sgbmzm/Halacha-T-S3/drivers/miriam25.py

# -*- coding: utf-8 -*-
# Converted from miriam.ttf using:
#     ./font2bitmap.py miriam.ttf -s 'abcdefghijklmnopqrstuvwxyzABCDEFGHIJKLMNOPQRSTUVWXYZ0123456789!#°{ }$%&'"'"'()*;<=>@#~^$!?+,-:./אבגדהוזחטיכךלמםנןסעפףצץקרשת' 25

MAP = (
    'abcdefghijklmnopqrstuvwxyzABCDEF'
    'GHIJKLMNOPQRSTUVWXYZ0123456789!#'
    '°{ }$%&\'()*;<=>@#~^$!?+,-:./אבג'
    'דהוזחטיכךלמםנןסעפףצץקרשת'
)

BPP = 1
HEIGHT = 23
MAX_WIDTH = 23
_WIDTHS = \
    b'\x0d\x0d\x0b\x0d\x0d\x07\x0d\x0d\x05\x07\x0b\x05\x13\x0d\x0d\x0d'\
    b'\x0d\x08\x0b\x06\x0d\x0b\x10\x0b\x0b\x0b\x0f\x0f\x10\x10\x0f\x0e'\
    b'\x12\x10\x06\x0b\x0f\x0d\x13\x10\x12\x0f\x12\x10\x0f\x0e\x10\x0f'\
    b'\x15\x0f\x0f\x0e\x0c\x0c\x0c\x0c\x0c\x0c\x0c\x0c\x0c\x0c\x07\x0a'\
    b'\x0a\x0c\x07\x0c\x0c\x12\x10\x07\x08\x08\x0c\x08\x0e\x0f\x0e\x17'\
    b'\x0a\x0e\x0a\x0c\x07\x09\x0f\x07\x07\x07\x07\x0a\x0f\x0d\x0a\x0c'\
    b'\x0f\x08\x08\x0e\x0e\x08\x0d\x0c\x0d\x0e\x0e\x08\x07\x0d\x0e\x0d'\
    b'\x0d\x0d\x0c\x0d\x0c\x10\x0f'

OFFSET_WIDTH = 2
_OFFSETS = \
    b'\x00\x00\x01\x2b\x02\x56\x03\x53\x04\x7e\x05\xa9\x06\x4a\x07\x75'\
    b'\x08\xa0\x09\x13\x09\xb4\x0a\xb1\x0b\x24\x0c\xd9\x0e\x04\x0f\x2f'\
    b'\x10\x5a\x11\x85\x12\x3d\x13\x3a\x13\xc4\x14\xef\x15\xec\x17\x5c'\
    b'\x18\x59\x19\x56\x1a\x53\x1b\xac\x1d\x05\x1e\x75\x1f\xe5\x21\x3e'\
    b'\x22\x80\x24\x1e\x25\x8e\x26\x18\x27\x15\x28\x6e\x29\x99\x2b\x4e'\
    b'\x2c\xbe\x2e\x5c\x2f\xb5\x31\x53\x32\xc3\x34\x1c\x35\x5e\x36\xce'\
    b'\x38\x27\x3a\x0a\x3b\x63\x3c\xbc\x3d\xfe\x3f\x12\x40\x26\x41\x3a'\
    b'\x42\x4e\x43\x62\x44\x76\x45\x8a\x46\x9e\x47\xb2\x48\xc6\x49\x67'\
    b'\x4a\x4d\x4b\x33\x4c\x47\x4c\xe8\x4d\xfc\x4f\x10\x50\xae\x52\x1e'\
    b'\x52\xbf\x53\x77\x54\x2f\x55\x43\x55\xfb\x57\x3d\x58\x96\x59\xd8'\
    b'\x5b\xe9\x5c\xcf\x5e\x11\x5e\xf7\x60\x0b\x60\xac\x61\x7b\x62\xd4'\
    b'\x63\x75\x64\x16\x64\xb7\x65\x58\x66\x3e\x67\x97\x68\xc2\x69\xa8'\
    b'\x6a\xbc\x6c\x15\x6c\xcd\x6d\x85\x6e\xc7\x70\x09\x70\xc1\x71\xec'\
    b'\x73\x00\x74\x2b\x75\x6d\x76\xaf\x77\x67\x78\x08\x79\x33\x7a\x75'\
    b'\x7b\xa0\x7c\xcb\x7d\xf6\x7f\x0a\x80\x35\x81\x49\x82\xb9'

_BITMAPS =\
    b'\x00\x00\x00\x00\x00\x00\x00\x00\x00\x00\x00\x03\xf0\x3f\xc3\x07'\
    b'\x00\x18\x3f\xc3\xfe\x38\x31\x81\x8c\x0c\x70\xe1\xfb\x07\x98\x00'\
    b'\x00\x00\x00\x00\x00\x00\x00\x00\x00\x00\x18\x00\xc0\x06\x00\x30'\
    b'\x01\x9e\x0f\xf8\x78\xe3\x83\x98\x0c\xc0\x66\x03\x30\x19\x81\xce'\
    b'\x1c\x7f\xc3\x3c\x00\x00\x00\x00\x00\x00\x00\x00\x00\x00\x00\x00'\
    b'\x00\x00\x00\x00\x01\xe0\xfe\x18\xe6\x0c\xc0\x18\x03\x00\x60\x0c'\
    b'\x18\xc3\x1f\xc0\xf0\x00\x00\x00\x00\x00\x00\x00\x00\x00\x00\x00'\
    b'\x18\x00\xc0\x06\x00\x30\x3d\x87\xfc\x30\xe3\x83\x18\x18\xc0\xc6'\
    b'\x06\x30\x31\xc1\x86\x1c\x1f\xe0\x7b\x00\x00\x00\x00\x00\x00\x00'\
    b'\x00\x00\x00\x00\x00\x00\x00\x00\x00\x00\x00\x07\xc0\x7f\x07\x1c'\
    b'\x60\x33\x01\x9f\xfc\xff\xe6\x00\x30\x18\xe1\xc3\xfc\x0f\x80\x00'\
    b'\x00\x00\x00\x00\x00\x00\x00\x00\x79\xf3\x06\x3f\x7e\x30\x60\xc1'\
    b'\x83\x06\x0c\x18\x30\x60\x00\x00\x00\x00\x00\x00\x00\x00\x00\x00'\
    b'\x00\x00\x00\x00\x00\x7b\x0f\xf8\x61\xc7\x0e\x30\x31\x81\x8c\x0c'\
    b'\x60\x63\x87\x0c\x38\x7f\xc0\xf6\x30\x31\xc3\x07\xf8\x1f\x00\x00'\
    b'\x00\x00\x00\x06\x00\x30\x01\x80\x0c\x00\x67\x83\xfe\x1c\x38\xc0'\
    b'\xc6\x06\x30\x31\x81\x8c\x0c\x60\x63\x03\x18\x18\xc0\xc0\x00\x00'\
    b'\x00\x00\x00\x00\x00\x00\xc6\x00\x0c\x63\x18\xc6\x31\x8c\x63\x18'\
    b'\x00\x00\x00\x00\x00\x18\x30\x00\x01\x83\x06\x0c\x18\x30\x60\xc1'\
    b'\x83\x06\x0c\x18\x33\xe7\x80\x00\x00\x00\x03\x00\x60\x0c\x01\x80'\
    b'\x30\xe6\x38\xce\x1b\x83\xe0\x7e\x0e\xc1\x8c\x31\xc6\x18\xc3\x98'\
    b'\x38\x00\x00\x00\x00\x00\x00\x00\x63\x18\xc6\x31\x8c\x63\x18\xc6'\
    b'\x31\x8c\x00\x00\x00\x00\x00\x00\x00\x00\x00\x00\x00\x00\x00\x00'\
    b'\x00\x00\x00\x00\x00\x37\xc7\x87\xfb\xf8\xe3\xc3\x98\x30\x33\x06'\
    b'\x06\x60\xc0\xcc\x18\x19\x83\x03\x30\x60\x66\x0c\x0c\xc1\x81\x98'\
    b'\x30\x30\x00\x00\x00\x00\x00\x00\x00\x00\x00\x00\x00\x00\x00\x00'\
    b'\x00\x00\x00\x00\x00\x00\x06\x78\x3f\xe1\xc3\x8c\x0c\x60\x63\x03'\
    b'\x18\x18\xc0\xc6\x06\x30\x31\x81\x8c\x0c\x00\x00\x00\x00\x00\x00'\
    b'\x00\x00\x00\x00\x00\x00\x00\x00\x00\x00\x00\x00\x1f\x03\xfc\x1c'\
    b'\x71\xc1\xcc\x06\x60\x33\x01\x98\x0c\xe0\xe3\x8e\x0f\xe0\x3e\x00'\
    b'\x00\x00\x00\x00\x00\x00\x00\x00\x00\x00\x00\x00\x00\x00\x00\x00'\
    b'\x00\x19\xe0\xff\x87\x8e\x38\x39\x80\xcc\x06\x60\x33\x01\x98\x1c'\
    b'\xe1\xc7\xfc\x37\xc1\x80\x0c\x00\x60\x03\x00\x00\x00\x00\x00\x00'\
    b'\x00\x00\x00\x00\x00\x00\x00\x7b\x07\xf8\x61\xc7\x06\x30\x31\x81'\
    b'\x8c\x0c\x60\x63\x83\x0e\x38\x3f\xc0\xf6\x00\x30\x01\x80\x0c\x00'\
    b'\x60\x00\x00\x00\x00\x00\x00\x03\x73\x83\x03\x03\x03\x03\x03\x03'\
    b'\x03\x03\x03\x00\x00\x00\x00\x00\x00\x00\x00\x00\x00\x00\x00\x00'\
    b'\x00\x07\xc1\xfe\x60\xcc\x01\xc0\x1f\x00\xf8\x03\x98\x33\x8e\x3f'\
    b'\x83\xe0\x00\x00\x00\x00\x00\x00\x00\x01\x0c\x30\xc7\xdf\x30\xc3'\
    b'\x0c\x30\xc3\x0c\x3c\x70\x00\x00\x00\x00\x00\x00\x00\x00\x00\x00'\
    b'\x00\x00\x00\x00\xc0\xc6\x06\x30\x31\x81\x8c\x0c\x60\x63\x03\x18'\
    b'\x18\xc0\xc7\x0e\x1f\xf0\x79\x80\x00\x00\x00\x00\x00\x00\x00\x00'\
    b'\x00\x00\x00\x00\x00\x00\x00\x0c\x06\xc1\x98\x33\x06\x31\x86\x30'\
    b'\xc6\x0d\x81\xb0\x14\x03\x80\x70\x00\x00\x00\x00\x00\x00\x00\x00'\
    b'\x00\x00\x00\x00\x00\x00\x00\x00\x00\x00\x00\x0c\x18\x3e\x18\x76'\
    b'\x3c\x66\x3c\x67\x2c\x63\x24\xc3\x26\xc3\xe6\xc1\xe7\x81\xe7\x81'\
    b'\xc3\x80\xc3\x00\x00\x00\x00\x00\x00\x00\x00\x00\x00\x00\x00\x00'\
    b'\x00\x00\x00\x00\x00\x38\x73\x0c\x33\x07\xe0\x78\x06\x01\xe0\x3c'\
    b'\x0c\xc1\x98\x61\x9c\x38\x00\x00\x00\x00\x00\x00\x00\x00\x00\x00'\
    b'\x00\x00\x00\x00\x03\x01\xb0\x66\x0c\x61\x8c\x21\x8c\x19\x83\x20'\
    b'\x3c\x07\x80\x60\x0c\x03\x80\x60\x7c\x0f\x00\x00\x00\x00\x00\x00'\
    b'\x00\x00\x00\x00\x0f\xf9\xff\x00\xe0\x18\x06\x01\x80\x60\x18\x06'\
    b'\x01\xc0\x3f\xe7\xfc\x00\x00\x00\x00\x00\x00\x00\x00\x00\x00\x00'\
    b'\x03\x80\x07\x00\x1e\x00\x36\x00\xec\x01\x8c\x03\x18\x0c\x38\x18'\
    b'\x30\x7f\xe0\xff\xe1\x80\xc7\x01\xcc\x01\x98\x03\x60\x07\x00\x00'\
    b'\x00\x00\x00\x00\x00\x00\x00\x00\x00\x00\x00\x1f\xf0\x3f\xf8\x60'\
    b'\x38\xc0\x31\x80\x63\x00\xc6\x03\x0f\xfc\x1f\xfc\x30\x1c\x60\x18'\
    b'\xc0\x31\x80\x63\x01\xc7\xff\x0f\xf8\x00\x00\x00\x00\x00\x00\x00'\
    b'\x00\x00\x00\x00\x00\x00\x00\x1f\x00\x7f\xc0\xe0\xe1\x80\x71\x80'\
    b'\x33\x00\x03\x00\x03\x00\x03\x00\x03\x00\x03\x00\x01\x80\x31\x80'\
    b'\x70\xe0\xe0\x7f\xc0\x3f\x00\x00\x00\x00\x00\x00\x00\x00\x00\x00'\
    b'\x00\x00\x00\x00\x01\xff\x01\xff\xc1\x81\xc1\x80\x61\x80\x61\x80'\
    b'\x31\x80\x31\x80\x31\x80\x31\x80\x31\x80\x31\x80\x61\x80\x61\x81'\
    b'\xc1\xff\xc1\xff\x00\x00\x00\x00\x00\x00\x00\x00\x00\x00\x00\x00'\
    b'\x00\x00\x0f\xff\x1f\xfe\x30\x00\x60\x00\xc0\x01\x80\x03\x00\x07'\
    b'\xff\x0f\xfe\x18\x00\x30\x00\x60\x00\xc0\x01\x80\x03\xff\xc7\xff'\
    b'\x80\x00\x00\x00\x00\x00\x00\x00\x00\x00\x00\x00\x00\x3f\xf8\xff'\
    b'\xe3\x00\x0c\x00\x30\x00\xc0\x03\x00\x0f\xf8\x3f\xe0\xc0\x03\x00'\
    b'\x0c\x00\x30\x00\xc0\x03\x00\x0c\x00\x00\x00\x00\x00\x00\x00\x00'\
    b'\x00\x00\x00\x00\x00\x00\x00\x0f\xe0\x0f\xfe\x07\x81\xc3\x80\x38'\
    b'\xc0\x06\x60\x00\x18\x00\x06\x00\x01\x80\xfe\x60\x3f\x98\x00\x63'\
    b'\x00\x18\xe0\x06\x1e\x07\x83\xff\xc0\x3f\x80\x00\x00\x00\x00\x00'\
    b'\x00\x00\x00\x00\x00\x00\x00\x00\x00\x00\xc0\x30\xc0\x30\xc0\x30'\
    b'\xc0\x30\xc0\x30\xc0\x30\xff\xf0\xff\xf0\xc0\x30\xc0\x30\xc0\x30'\
    b'\xc0\x30\xc0\x30\xc0\x30\xc0\x30\xc0\x30\x00\x00\x00\x00\x00\x00'\
    b'\x00\x00\x00\x00\x30\xc3\x0c\x30\xc3\x0c\x30\xc3\x0c\x30\xc3\x0c'\
    b'\x00\x00\x00\x00\x00\x00\x00\x00\xc0\x18\x03\x00\x60\x0c\x01\x80'\
    b'\x30\x06\x00\xc0\x18\x03\x18\x63\x0c\x63\x87\xe0\x78\x00\x00\x00'\
    b'\x00\x00\x00\x00\x00\x00\x00\x00\x0c\x07\x18\x1c\x30\x70\x61\xc0'\
    b'\xc7\x01\x9c\x03\x70\x07\xf0\x0f\x70\x1c\x60\x30\xe0\x60\xe0\xc0'\
    b'\xc1\x81\xc3\x01\xc6\x01\xc0\x00\x00\x00\x00\x00\x00\x00\x00\x00'\
    b'\x00\x00\x01\x80\x0c\x00\x60\x03\x00\x18\x00\xc0\x06\x00\x30\x01'\
    b'\x80\x0c\x00\x60\x03\x00\x18\x00\xc0\x07\xfe\x3f\xf0\x00\x00\x00'\
    b'\x00\x00\x00\x00\x00\x00\x00\x00\x00\x00\x1c\x00\x73\xc0\x1e\x78'\
    b'\x03\xcf\x00\x79\xb0\x1b\x36\x03\x66\x60\xcc\xcc\x19\x99\x83\x33'\
    b'\x18\xc6\x63\x18\xcc\x32\x19\x86\xc3\x30\xd8\x66\x0e\x0c\xc1\xc1'\
    b'\x80\x00\x00\x00\x00\x00\x00\x00\x00\x00\x00\x00\x00\x00\x00\x00'\
    b'\xc0\x30\xe0\x30\xf0\x30\xf0\x30\xd8\x30\xc8\x30\xcc\x30\xc6\x30'\
    b'\xc6\x30\xc3\x30\xc1\x30\xc1\xb0\xc0\xf0\xc0\xf0\xc0\x70\xc0\x30'\
    b'\x00\x00\x00\x00\x00\x00\x00\x00\x00\x00\x00\x00\x00\x00\x00\x3f'\
    b'\x00\x3f\xf0\x1c\x0e\x0e\x01\xc3\x00\x31\x80\x06\x60\x01\x98\x00'\
    b'\x66\x00\x19\x80\x06\x60\x01\x8c\x00\xc3\x80\x70\x70\x38\x0f\xfc'\
    b'\x00\xfc\x00\x00\x00\x00\x00\x00\x00\x00\x00\x00\x00\x00\x00\x00'\
    b'\x00\x1f\xf8\x3f\xf8\x60\x38\xc0\x31\x80\x63\x00\xc6\x03\x8f\xfe'\
    b'\x1f\xf0\x30\x00\x60\x00\xc0\x01\x80\x03\x00\x06\x00\x0c\x00\x00'\
    b'\x00\x00\x00\x00\x00\x00\x00\x00\x00\x00\x00\x00\x00\x00\x7e\x00'\
    b'\x7f\xe0\x38\x1c\x1c\x03\x86\x00\x63\x00\x0c\xc0\x03\x30\x00\xcc'\
    b'\x00\x33\x00\x0c\xc0\x03\x18\x0d\x87\x03\xe0\xf0\x30\x1f\xfe\x01'\
    b'\xf9\xe0\x00\x18\x00\x00\x00\x00\x00\x00\x00\x00\x00\x00\x00\x00'\
    b'\x07\xfe\x07\xff\x06\x03\x86\x01\x86\x01\x86\x01\x86\x03\x07\xff'\
    b'\x07\xfc\x06\x18\x06\x0c\x06\x06\x06\x03\x06\x03\x06\x01\x86\x00'\
    b'\xc0\x00\x00\x00\x00\x00\x00\x00\x00\x00\x00\x00\x00\x00\x07\xe0'\
    b'\x3f\xf0\xe0\x71\x80\x63\x00\x06\x00\x07\x00\x0f\xe0\x07\xf0\x00'\
    b'\xf0\x00\x31\x80\x63\x80\xc3\x83\x03\xfe\x03\xf0\x00\x00\x00\x00'\
    b'\x00\x00\x00\x00\x00\x00\x00\x00\x01\xff\xe7\xff\x80\xc0\x03\x00'\
    b'\x0c\x00\x30\x00\xc0\x03\x00\x0c\x00\x30\x00\xc0\x03\x00\x0c\x00'\
    b'\x30\x00\xc0\x03\x00\x00\x00\x00\x00\x00\x00\x00\x00\x00\x00\x00'\
    b'\x00\x00\xc0\x30\xc0\x30\xc0\x30\xc0\x30\xc0\x30\xc0\x30\xc0\x30'\
    b'\xc0\x30\xc0\x30\xc0\x30\xc0\x30\xc0\x30\xe0\x70\x70\xe0\x7f\xc0'\
    b'\x1f\x80\x00\x00\x00\x00\x00\x00\x00\x00\x00\x00\x00\x00\x00\x18'\
    b'\x00\xd8\x03\x30\x06\x60\x18\x60\x30\xc0\x61\x81\x81\x83\x03\x0c'\
    b'\x02\x18\x06\x60\x0c\xc0\x0d\x80\x1e\x00\x3c\x00\x30\x00\x00\x00'\
    b'\x00\x00\x00\x00\x00\x00\x00\x00\x00\x00\x00\x00\x03\x00\xc0\x78'\
    b'\x0e\x03\x60\x78\x33\x02\xc1\x98\x32\x0c\xc1\x98\x62\x08\xc2\x18'\
    b'\xc2\x30\xc6\x19\x86\x60\xcc\x13\x06\x40\x98\x16\x07\x80\xf0\x3c'\
    b'\x07\x80\xe0\x18\x06\x00\xc0\x00\x00\x00\x00\x00\x00\x00\x00\x00'\
    b'\x00\x00\x00\x00\x00\x00\x00\xe0\x1c\xe0\x70\xe1\xc0\xc3\x00\xcc'\
    b'\x01\xf8\x01\xe0\x01\x80\x07\x80\x0f\x00\x33\x00\xe7\x01\x87\x06'\
    b'\x06\x1c\x0e\x70\x0e\x00\x00\x00\x00\x00\x00\x00\x00\x00\x00\x00'\
    b'\x00\x00\xc0\x0c\xc0\x30\xc0\xc1\xc3\x81\x86\x01\x98\x03\xf0\x03'\
    b'\xc0\x03\x00\x06\x00\x0c\x00\x18\x00\x30\x00\x60\x00\xc0\x01\x80'\
    b'\x00\x00\x00\x00\x00\x00\x00\x00\x00\x00\x00\x00\x01\xff\xe7\xff'\
    b'\x80\x0e\x00\x30\x01\x80\x0c\x00\x60\x03\x00\x1c\x00\x60\x03\x00'\
    b'\x18\x00\xc0\x06\x00\x1f\xfe\x7f\xf8\x00\x00\x00\x00\x00\x00\x00'\
    b'\x00\x00\x00\x00\x00\x00\x00\x03\xe0\xff\x0e\x71\xc3\x98\x19\x81'\
    b'\x98\x19\x81\x98\x19\x81\x9c\x38\xe7\x0f\xf0\x7e\x00\x00\x00\x00'\
    b'\x00\x00\x00\x00\x00\x00\x00\x00\x00\x00\x18\x03\x80\x78\x0f\x80'\
    b'\xd8\x01\x80\x18\x01\x80\x18\x01\x80\x18\x01\x80\x18\x01\x80\x00'\
    b'\x00\x00\x00\x00\x00\x00\x00\x00\x00\x00\x00\x00\x03\xc0\xfe\x1c'\
    b'\x71\x83\x00\x30\x03\x00\x60\x0c\x01\x80\x30\x06\x00\x40\x0f\xf0'\
    b'\xff\x00\x00\x00\x00\x00\x00\x00\x00\x00\x00\x00\x00\x00\x00\xfe'\
    b'\x0f\xe0\x04\x00\x80\x10\x03\xc0\x7e\x06\x70\x03\x00\x31\x03\x18'\
    b'\x60\xfe\x07\x80\x00\x00\x00\x00\x00\x00\x00\x00\x00\x00\x00\x00'\
    b'\x00\x00\xe0\x3e\x03\x60\x66\x04\x60\x46\x0c\x60\x86\x1f\xf9\xff'\
    b'\x80\x60\x06\x00\x60\x06\x00\x00\x00\x00\x00\x00\x00\x00\x00\x00'\
    b'\x00\x00\x00\x00\xfe\x0f\xe0\x80\x18\x01\xfc\x1f\xe1\x86\x00\x30'\
    b'\x03\x00\x30\x03\x18\x61\xfe\x07\xc0\x00\x00\x00\x00\x00\x00\x00'\
    b'\x00\x00\x00\x00\x00\x00\x00\xf0\x3f\x07\x00\xc0\x0b\xe1\xff\x1c'\
    b'\x31\x81\x98\x19\x81\x98\x18\xc3\x0f\xf0\x3c\x00\x00\x00\x00\x00'\
    b'\x00\x00\x00\x00\x00\x00\x00\x00\x01\xff\x1f\xf0\x03\x00\x60\x06'\
    b'\x00\xc0\x08\x01\x80\x10\x03\x00\x30\x06\x00\x60\x06\x00\x00\x00'\
    b'\x00\x00\x00\x00\x00\x00\x00\x00\x00\x00\x00\x03\xc0\xff\x0e\x70'\
    b'\xc3\x0e\x70\x7e\x0f\xf1\xc3\x98\x19\x81\x98\x19\xc3\x8f\xf0\x3c'\
    b'\x00\x00\x00\x00\x00\x00\x00\x00\x00\x00\x00\x00\x00\x00\x3c\x0f'\
    b'\xf0\xc3\x18\x19\x81\x98\x19\x81\x8c\x38\xff\x87\xd0\x03\x00\xe0'\
    b'\xfc\x0f\x00\x00\x00\x00\x00\x00\x00\x00\x00\x00\x0c\x18\x30\x60'\
    b'\xc1\x83\x06\x0c\x18\x30\x00\x01\x83\x00\x00\x00\x00\x00\x00\x00'\
    b'\x00\x00\x00\x04\x41\x10\x44\x11\x04\x5f\xf8\x88\x22\x08\x9f\xf9'\
    b'\x10\x44\x22\x08\x80\x00\x00\x00\x00\x00\x00\x00\x00\x03\xc1\x08'\
    b'\x81\x20\x48\x12\x04\x42\x0f\x00\x00\x00\x00\x00\x00\x00\x00\x00'\
    b'\x00\x00\x00\x00\x00\x00\x00\x00\x00\x00\x30\x06\x00\xc0\x0c\x00'\
    b'\xc0\x0c\x00\xc0\x0c\x00\xc0\x0c\x03\x00\x0c\x00\xc0\x0c\x00\xc0'\
    b'\x0c\x00\xc0\x0c\x00\xc0\x06\x00\x30\x00\x00\x00\x00\x00\x00\x00'\
    b'\x00\x00\x00\x00\x00\x00\x00\x00\x00\x00\x00\x00\x00\x00\x00\x00'\
    b'\x0c\x00\x60\x06\x00\x60\x06\x00\x60\x06\x00\x60\x06\x00\x60\x01'\
    b'\x80\x60\x06\x00\x60\x06\x00\x60\x06\x00\x60\x06\x00\x60\x0c\x00'\
    b'\x00\x00\x00\x00\x00\x00\x40\x1f\x03\xf8\x74\xc6\x44\x64\x07\x40'\
    b'\x3f\x00\xfc\x04\xe0\x46\x84\x6e\x4e\x7f\xc1\xf0\x04\x00\x40\x00'\
    b'\x00\x00\x00\x00\x00\x00\x00\x00\x00\x00\x00\x00\x04\x07\x02\x03'\
    b'\xe1\x81\x8c\x40\x63\x30\x18\xc8\x03\xe4\x00\x73\x00\x00\x8e\x00'\
    b'\x47\xc0\x33\x18\x08\xc6\x06\x31\x81\x07\xc0\x80\xe0\x00\x00\x00'\
    b'\x00\x00\x00\x00\x00\x00\x00\x00\x00\x00\x00\x00\x00\x00\x0e\x00'\
    b'\x19\x00\x31\x00\x31\x00\x32\x00\x14\x00\x18\xf0\x3c\x60\xcc\x40'\
    b'\x8e\x81\x86\x81\x87\x01\x83\x89\xc5\xf0\xf8\xe0\x00\x00\x00\x00'\
    b'\x00\x00\x00\x00\x00\x00\x00\x00\x0c\x18\x20\xc1\x00\x00\x00\x00'\
    b'\x00\x00\x00\x00\x00\x00\x00\x00\x00\x00\x00\x00\x0c\x18\x10\x20'\
    b'\x20\x60\x40\x40\x40\x40\x40\x40\x60\x20\x20\x10\x18\x0c\x00\x00'\
    b'\x00\x00\x00\xc0\x60\x20\x10\x10\x18\x08\x08\x08\x08\x08\x08\x18'\
    b'\x10\x10\x20\x60\xc0\x00\x0c\x00\xc0\xc8\x8e\x9c\x3f\x00\xc0\x3f'\
    b'\x0e\x9c\x88\x80\xc0\x0c\x00\x00\x00\x00\x00\x00\x00\x00\x00\x00'\
    b'\x00\x00\x00\x00\x00\x00\x00\x00\x00\x00\x00\x00\x00\x00\x00\x00'\
    b'\x03\x03\x00\x00\x00\x00\x00\x03\x06\x06\x0c\x0c\x00\x00\x00\x00'\
    b'\x00\x00\x00\x00\x00\x00\x00\x00\x00\x00\x00\x00\x00\x00\x01\x00'\
    b'\x3c\x03\xc0\x38\x07\x80\x18\x00\x3c\x00\x3c\x00\x3c\x00\x1c\x00'\
    b'\x10\x00\x00\x00\x00\x00\x00\x00\x00\x00\x00\x00\x00\x00\x00\x00'\
    b'\x00\x00\x00\x00\x00\x00\x00\x00\x00\x00\x00\x00\x0f\xff\x1f\xfe'\
    b'\x00\x00\x00\x00\xff\xf1\xff\xe0\x00\x00\x00\x00\x00\x00\x00\x00'\
    b'\x00\x00\x00\x00\x00\x00\x00\x00\x00\x00\x00\x00\x00\x00\x00\x00'\
    b'\x00\x80\x03\xc0\x03\xc0\x03\xc0\x01\xc0\x01\x80\x1e\x01\xc0\x3c'\
    b'\x03\xc0\x08\x00\x00\x00\x00\x00\x00\x00\x00\x00\x00\x00\x00\x00'\
    b'\x00\x00\x00\x00\x03\xf8\x00\x3f\xfc\x00\xf0\x3e\x03\x80\x1c\x0c'\
    b'\x3c\xcc\x39\xfd\x9c\x63\x8e\x19\xcc\x0c\x33\x38\x18\x66\x60\x30'\
    b'\xcc\xc0\x41\x99\x81\x86\x33\x03\x1c\x73\x1e\x70\x67\xef\xc0\xe7'\
    b'\x8e\x30\xe0\x01\xc0\xf8\x0f\x00\x7f\xfc\x00\x1f\xe0\x00\x00\x00'\
    b'\x00\x00\x00\x01\x10\x44\x11\x04\x41\x17\xfe\x22\x08\x82\x27\xfe'\
    b'\x44\x11\x08\x82\x20\x00\x00\x00\x00\x00\x00\x00\x00\x00\x00\x00'\
    b'\x00\x00\x00\x00\x00\x00\x00\x00\x00\x00\x00\x07\x03\x3f\x8d\x8f'\
    b'\xe4\x0f\x00\x00\x00\x00\x00\x00\x00\x00\x00\x00\x00\x00\x00\x00'\
    b'\x00\x00\x00\x00\x00\x00\x00\x00\x01\x00\xa0\x28\x11\x04\x42\x08'\
    b'\x82\x40\x40\x00\x00\x00\x00\x00\x00\x00\x00\x00\x00\x00\x00\x00'\
    b'\x00\x00\x00\x00\x00\x08\x03\xe0\x7f\x0e\x98\xc8\x8c\x80\xe8\x07'\
    b'\xe0\x1f\x80\x9c\x08\xd0\x8d\xc9\xcf\xf8\x3e\x00\x80\x08\x00\x00'\
    b'\x00\x00\x00\x00\x00\x60\xc1\x83\x06\x0c\x18\x30\x60\xc1\x80\x00'\
    b'\x0c\x18\x00\x00\x00\x00\x00\x00\x00\x00\x38\x3e\x31\x98\xc0\x60'\
    b'\x30\x30\x18\x1c\x0c\x06\x03\x00\x00\xc0\x60\x00\x00\x00\x00\x00'\
    b'\x00\x00\x00\x00\x00\x00\x00\x00\x00\x00\x00\x00\x00\x18\x00\x30'\
    b'\x00\x60\x00\xc0\x01\x80\x7f\xf8\xff\xf0\x0c\x00\x18\x00\x30\x00'\
    b'\x60\x00\xc0\x00\x00\x00\x00\x00\x00\x00\x00\x00\x00\x00\x00\x00'\
    b'\x00\x00\x00\x00\x00\x00\x00\x00\xc3\x06\x18\x30\x00\x00\x00\x00'\
    b'\x00\x00\x00\x00\x00\x00\x00\x00\x1f\x3e\x00\x00\x00\x00\x00\x00'\
    b'\x00\x00\x00\x00\x00\x00\x00\x00\x00\x00\x00\xc1\x80\x00\x00\x00'\
    b'\x00\x00\xc1\x80\x00\x00\x00\x00\x00\x00\x00\x00\x00\x00\x00\x00'\
    b'\x00\x00\x00\x00\x00\x00\x60\xc0\x00\x00\x00\x00\x00\x60\x10\x04'\
    b'\x03\x00\x80\x60\x18\x04\x03\x00\x80\x20\x18\x04\x03\x00\x80\x20'\
    b'\x18\x04\x01\x00\xc0\x00\x00\x00\x00\x00\x00\x00\x00\x00\x00\x00'\
    b'\x00\x18\x38\x18\x78\x18\x30\x10\x60\x30\xc0\xf1\x83\x66\x0c\x78'\
    b'\x18\x60\x30\x40\x60\xc0\xc0\xc1\xe0\xc1\xc0\xc0\x00\x00\x00\x00'\
    b'\x00\x00\x00\x00\x00\x00\x00\x00\x00\x00\x00\x3f\xc1\xff\x00\x18'\
    b'\x00\xc0\x06\x00\x30\x01\x80\x0c\x00\x60\x03\x00\x18\x00\xc7\xff'\
    b'\xbf\xfc\x00\x00\x00\x00\x00\x00\x00\x00\x00\x00\x00\x00\x01\xf0'\
    b'\x7c\x03\x00\xc0\x30\x0c\x03\x00\xc0\x30\x1c\x0f\x06\xc7\x33\x0c'\
    b'\x00\x00\x00\x00\x00\x00\x00\x00\x00\x00\x00\x00\x07\xff\x7f\xf0'\
    b'\x18\x01\x80\x18\x01\x80\x18\x01\x80\x18\x01\x80\x18\x01\x80\x18'\
    b'\x01\x80\x00\x00\x00\x00\x00\x00\x00\x00\x00\x00\x00\x00\x00\x00'\
    b'\x00\x7f\xe0\xff\xc0\x01\x80\x03\x06\x06\x0c\x0c\x18\x18\x30\x30'\
    b'\x60\x60\xc0\xc1\x81\x83\x03\x06\x06\x0c\x0c\x00\x00\x00\x00\x00'\
    b'\x00\x00\x00\x00\x00\x00\x00\x07\xe7\xe0\x60\x60\x60\x60\x60\x60'\
    b'\x60\x60\x60\x60\x60\x60\x00\x00\x00\x00\x00\x00\x00\x00\x03\xf3'\
    b'\xf0\xc0\xc0\xc0\xc0\xc0\xc0\xc0\xc0\xc0\xc0\xc0\xc0\x00\x00\x00'\
    b'\x00\x00\x00\x00\x00\x00\x00\x00\x00\x0f\xfe\x3f\xf8\x30\x60\xc1'\
    b'\x83\x06\x0c\x18\x30\x60\xc1\x83\x06\x0c\x18\x30\x60\xc1\x83\x06'\
    b'\x0c\x18\x00\x00\x00\x00\x00\x00\x00\x00\x00\x00\x00\x00\x00\x00'\
    b'\x00\x07\x9f\x1e\xfe\x1b\x18\x6c\x61\xb1\x86\xc6\x18\x18\x60\x61'\
    b'\x81\x86\x06\x18\x18\x70\x60\xff\x81\xf8\x00\x00\x00\x00\x00\x00'\
    b'\x00\x00\x00\x00\x00\x00\x3f\x3f\x03\x03\x03\x03\x03\x00\x00\x00'\
    b'\x00\x00\x00\x00\x00\x00\x00\x00\x00\x00\x00\x00\x00\x00\x00\x00'\
    b'\x1f\xe0\xff\x80\x0e\x00\x30\x01\x80\x0c\x00\x60\x03\x00\x18\x00'\
    b'\xc0\x06\x00\x31\xff\x8f\xf8\x00\x00\x00\x00\x00\x00\x00\x00\x00'\
    b'\x00\x00\x00\x00\x00\xff\x8f\xf8\x01\x80\x18\x01\x80\x18\x01\x80'\
    b'\x18\x01\x80\x18\x01\x80\x18\x01\x80\x18\x01\x80\x18\x01\x80\x00'\
    b'\x00\x00\x00\x18\x00\xc0\x06\x00\x3f\xf1\xff\x80\x0c\x00\x60\x03'\
    b'\x00\x18\x01\xc0\x1c\x01\xc0\x1c\x00\xc0\x0c\x00\x60\x03\x00\x00'\
    b'\x00\x00\x00\x00\x00\x00\x00\x00\x00\x00\x00\x00\x00\x00\x3c\xf0'\
    b'\xff\xe0\xf3\x83\x86\x0c\x18\x30\x60\xc1\x83\x06\x0c\x18\x30\x60'\
    b'\xc1\x83\x06\x0c\xf8\x33\xe0\x00\x00\x00\x00\x00\x00\x00\x00\x00'\
    b'\x00\x00\x00\x00\x00\x00\x0f\xfe\x3f\xf8\x30\x60\xc1\x83\x06\x0c'\
    b'\x18\x30\x60\xc1\x83\x06\x0c\x18\x30\x60\xc1\x83\xfe\x0f\xf8\x00'\
    b'\x00\x00\x00\x00\x00\x00\x00\x00\x00\x00\x00\xf8\xf8\x18\x18\x18'\
    b'\x18\x18\x18\x18\x18\x18\x18\xf8\xf8\x00\x00\x00\x00\x00\x00\x00'\
    b'\x00\x1e\x3c\x18\x30\x60\xc1\x83\x06\x0c\x18\x30\x60\xc1\x83\x06'\
    b'\x00\x00\x00\x00\x00\x00\x00\x00\x00\x7f\xe3\xff\x86\x0c\x30\x61'\
    b'\x83\x0c\x18\x60\xc3\x06\x18\x30\xc1\x86\x0c\x38\xe0\xfe\x03\xe0'\
    b'\x00\x00\x00\x00\x00\x00\x00\x00\x00\x00\x00\x00\x00\x00\x00\x7c'\
    b'\x79\xf1\xe0\xc1\x83\x06\x0c\x18\x30\x60\xc1\x83\x06\x0c\x18\x30'\
    b'\x60\xc1\x83\x1c\x7f\xe1\xff\x00\x00\x00\x00\x00\x00\x00\x00\x00'\
    b'\x00\x00\x00\x00\x00\x00\x00\xff\x87\xfc\x30\x61\x83\x0c\x18\x60'\
    b'\xc3\xe6\x1f\x30\x01\x80\x0c\x00\x60\x03\x0f\xf8\x7f\x80\x00\x00'\
    b'\x00\x00\x00\x00\x00\x00\x00\x00\x00\x00\x00\x00\x1f\xf0\xff\x86'\
    b'\x0c\x30\x61\x83\x0c\x18\x60\xc3\xe6\x1f\x30\x01\x80\x0c\x00\x60'\
    b'\x03\x00\x18\x00\xc0\x06\x00\x30\x00\x00\x00\x00\x00\x00\x00\x00'\
    b'\x00\x07\x8f\x3c\x78\x60\xc3\x06\x18\x60\x67\x01\xf0\x07\x00\x1c'\
    b'\x00\x30\x00\xc0\x06\x7f\xf3\xff\x80\x00\x00\x00\x00\x00\x00\x00'\
    b'\x00\x00\x00\x00\x00\x00\x3c\x7b\xc7\x8c\x18\xc1\x8c\x38\xc3\x0c'\
    b'\xe0\xfc\x0f\x80\xc0\x0c\x00\xc0\x0c\x00\xc0\x0c\x00\xc0\x0c\x00'\
    b'\x00\x00\x00\x00\x00\x00\x00\x00\x00\x0f\xfe\x7f\xf0\x01\x80\x0c'\
    b'\x60\x63\x03\x18\x38\xc3\x86\x18\x31\xc1\x9c\x0c\xc0\x66\x03\x30'\
    b'\x18\x00\xc0\x06\x00\x00\x00\x00\x00\x00\x00\x00\x00\x00\x3f\xe3'\
    b'\xfe\x00\x60\x06\x00\x60\x06\x00\x60\x06\x00\x60\x06\x00\x60\x06'\
    b'\x00\x60\x06\x00\x00\x00\x00\x00\x00\x00\x00\x00\x00\x00\x00\x00'\
    b'\x00\x00\x00\x1c\xce\x1c\xce\x18\xc6\x18\xc6\x18\xc6\x18\xc6\x18'\
    b'\xc6\x18\xc6\x18\xc6\x18\xc6\x18\xc6\x18\xc6\x1f\xfe\x0f\xfc\x00'\
    b'\x00\x00\x00\x00\x00\x00\x00\x00\x00\x00\x00\x00\x00\x00\x00\x00'\
    b'\x07\xff\x8f\xff\x06\x06\x0c\x0c\x18\x18\x30\x30\x60\x60\xc0\xc1'\
    b'\x81\x83\x03\x06\x06\x0c\x0c\x78\x18\xf0\x30\x00\x00\x00\x00\x00'\
    b'\x00\x00\x00'

WIDTHS = memoryview(_WIDTHS)
OFFSETS = memoryview(_OFFSETS)
BITMAPS = memoryview(_BITMAPS)
