sgbmzm/Halacha-T-S3/drivers/miriam30.py

# -*- coding: utf-8 -*-
# Converted from miriam.ttf using:
#     ./font2bitmap.py miriam.ttf -s 'abcdefghijklmnopqrstuvwxyzABCDEFGHIJKLMNOPQRSTUVWXYZ0123456789!#°{ }$%&'"'"'()*;<=>@#~^$!?+,-:./אבגדהוזחטיכךלמםנןסעפףצץקרשת' 30

MAP = (
    'abcdefghijklmnopqrstuvwxyzABCDEF'
    'GHIJKLMNOPQRSTUVWXYZ0123456789!#'
    '°{ }$%&\'()*;<=>@#~^$!?+,-:./אבג'
    'דהוזחטיכךלמםנןסעפףצץקרשת'
)

BPP = 1
HEIGHT = 28
MAX_WIDTH = 27
_WIDTHS = \
    b'\x0f\x0f\x0e\x0f\x0f\x08\x0f\x0f\x06\x07\x0e\x06\x16\x0f\x0f\x0f'\
    b'\x0f\x09\x0e\x08\x0f\x0e\x14\x0e\x0e\x0e\x12\x12\x14\x14\x12\x11'\
    b'\x15\x14\x08\x0e\x12\x0f\x16\x14\x15\x12\x15\x14\x12\x11\x14\x12'\
    b'\x19\x13\x12\x11\x0e\x0e\x0e\x0e\x0e\x0e\x0e\x0e\x0e\x0e\x08\x0c'\
    b'\x0c\x0e\x08\x0e\x0e\x16\x13\x08\x09\x09\x0f\x09\x11\x12\x11\x1b'\
    b'\x0c\x10\x0c\x0e\x08\x0b\x12\x08\x08\x08\x08\x0c\x11\x10\x0c\x0e'\
    b'\x11\x0a\x09\x11\x11\x0a\x10\x0e\x10\x11\x11\x0a\x09\x10\x11\x10'\
    b'\x10\x10\x0f\x10\x0e\x13\x11'

OFFSET_WIDTH = 2
_OFFSETS = \
    b'\x00\x00\x01\xa4\x03\x48\x04\xd0\x06\x74\x08\x18\x08\xf8\x0a\x9c'\
    b'\x0c\x40\x0c\xe8\x0d\xac\x0f\x34\x0f\xdc\x12\x44\x13\xe8\x15\x8c'\
    b'\x17\x30\x18\xd4\x19\xd0\x1b\x58\x1c\x38\x1d\xdc\x1f\x64\x21\x94'\
    b'\x23\x1c\x24\xa4\x26\x2c\x28\x24\x2a\x1c\x2c\x4c\x2e\x7c\x30\x74'\
    b'\x32\x50\x34\x9c\x36\xcc\x37\xac\x39\x34\x3b\x2c\x3c\xd0\x3f\x38'\
    b'\x41\x68\x43\xb4\x45\xac\x47\xf8\x4a\x28\x4c\x20\x4d\xfc\x50\x2c'\
    b'\x52\x24\x54\xe0\x56\xf4\x58\xec\x5a\xc8\x5c\x50\x5d\xd8\x5f\x60'\
    b'\x60\xe8\x62\x70\x63\xf8\x65\x80\x67\x08\x68\x90\x6a\x18\x6a\xf8'\
    b'\x6c\x48\x6d\x98\x6f\x20\x70\x00\x71\x88\x73\x10\x75\x78\x77\x8c'\
    b'\x78\x6c\x79\x68\x7a\x64\x7c\x08\x7d\x04\x7e\xe0\x80\xd8\x82\xb4'\
    b'\x85\xa8\x86\xf8\x88\xb8\x8a\x08\x8b\x90\x8c\x70\x8d\xa4\x8f\x9c'\
    b'\x90\x7c\x91\x5c\x92\x3c\x93\x1c\x94\x6c\x96\x48\x98\x08\x99\x58'\
    b'\x9a\xe0\x9c\xbc\x9d\xd4\x9e\xd0\xa0\xac\xa2\x88\xa3\xa0\xa5\x60'\
    b'\xa6\xe8\xa8\xa8\xaa\x84\xac\x60\xad\x78\xae\x74\xb0\x34\xb2\x10'\
    b'\xb3\xd0\xb5\x90\xb7\x50\xb8\xf4\xba\xb4\xbc\x3c\xbe\x50'

_BITMAPS =\
    b'\x00\x00\x00\x00\x00\x00\x00\x00\x00\x00\x00\x00\x00\x00\x00\x00'\
    b'\x00\x1f\xc0\xff\xc3\x81\xc6\x01\x80\x03\x03\xfe\x1f\xfc\x38\x18'\
    b'\xc0\x31\x80\x63\x01\xc7\x07\x87\xfd\x07\xe3\x00\x00\x00\x00\x00'\
    b'\x00\x00\x00\x00\x00\x00\x00\x00\x00\x00\x00\x00\x30\x00\x60\x00'\
    b'\xc0\x01\x80\x03\x00\x06\x7c\x0f\xfc\x1e\x1c\x38\x18\x60\x18\xc0'\
    b'\x31\x80\x63\x00\xc6\x01\x8c\x03\x1c\x0c\x3c\x38\x7f\xe0\xcf\x00'\
    b'\x00\x00\x00\x00\x00\x00\x00\x00\x00\x00\x00\x00\x00\x00\x00\x00'\
    b'\x00\x00\x00\x00\x00\x00\x00\x00\x00\x3e\x01\xfe\x0e\x38\x30\x71'\
    b'\x80\xc6\x00\x18\x00\x60\x01\x80\x06\x03\x0c\x1c\x38\xe0\x7f\x00'\
    b'\xf8\x00\x00\x00\x00\x00\x00\x00\x00\x00\x00\x00\x00\x00\x00\x00'\
    b'\x00\x00\x01\x80\x03\x00\x06\x00\x0c\x00\x18\x0f\x30\x7f\xe1\xc3'\
    b'\xc3\x03\x8c\x03\x18\x06\x30\x0c\x60\x18\xc0\x31\x80\x61\x81\xc3'\
    b'\x87\x83\xff\x01\xe6\x00\x00\x00\x00\x00\x00\x00\x00\x00\x00\x00'\
    b'\x00\x00\x00\x00\x00\x00\x00\x00\x00\x00\x00\x00\x00\x00\x00\x00'\
    b'\xf8\x07\xfc\x1c\x1c\x30\x18\xc0\x19\x80\x33\xff\xe7\xff\xcc\x00'\
    b'\x18\x00\x18\x06\x38\x38\x3f\xf0\x1f\x80\x00\x00\x00\x00\x00\x00'\
    b'\x00\x00\x00\x00\x00\x00\x00\x0f\x1f\x18\x18\x18\x7f\x7f\x18\x18'\
    b'\x18\x18\x18\x18\x18\x18\x18\x18\x18\x18\x00\x00\x00\x00\x00\x00'\
    b'\x00\x00\x00\x00\x00\x00\x00\x00\x00\x00\x00\x00\x00\x00\x00\x00'\
    b'\x0f\x30\x7f\xe1\xc3\xc3\x03\x8c\x03\x18\x06\x30\x0c\x60\x18\xc0'\
    b'\x31\x80\x61\x81\xc3\x87\x83\xff\x01\xe6\x30\x0c\x60\x38\xe0\xe0'\
    b'\xff\x80\x7e\x00\x00\x00\x00\x00\x00\x00\x00\x30\x00\x60\x00\xc0'\
    b'\x01\x80\x03\x00\x06\x7c\x0f\xfc\x1e\x1c\x38\x18\x60\x30\xc0\x61'\
    b'\x80\xc3\x01\x86\x03\x0c\x06\x18\x0c\x30\x18\x60\x30\xc0\x60\x00'\
    b'\x00\x00\x00\x00\x00\x00\x00\x00\x00\x00\x00\x30\xc3\x00\x00\xc3'\
    b'\x0c\x30\xc3\x0c\x30\xc3\x0c\x30\xc3\x00\x00\x00\x00\x00\x00\x00'\
    b'\x01\x83\x06\x00\x00\x30\x60\xc1\x83\x06\x0c\x18\x30\x60\xc1\x83'\
    b'\x06\x0c\x18\x33\xe7\x80\x00\x00\x00\x00\x00\x00\x03\x00\x0c\x00'\
    b'\x30\x00\xc0\x03\x00\x0c\x1e\x30\xf0\xc7\x83\x3c\x0d\xe0\x3f\x00'\
    b'\xfe\x03\xbc\x0c\x70\x30\xe0\xc3\xc3\x07\x0c\x0e\x30\x3c\x00\x00'\
    b'\x00\x00\x00\x00\x00\x00\x00\x00\x00\x03\x0c\x30\xc3\x0c\x30\xc3'\
    b'\x0c\x30\xc3\x0c\x30\xc3\x0c\x30\x00\x00\x00\x00\x00\x00\x00\x00'\
    b'\x00\x00\x00\x00\x00\x00\x00\x00\x00\x00\x00\x00\x00\x00\x00\x00'\
    b'\x00\x00\x00\x00\x0c\xf0\xf0\x3f\xef\xe0\xf1\xf1\xc3\x83\x83\x0c'\
    b'\x0c\x0c\x30\x30\x30\xc0\xc0\xc3\x03\x03\x0c\x0c\x0c\x30\x30\x30'\
    b'\xc0\xc0\xc3\x03\x03\x0c\x0c\x0c\x30\x30\x30\x00\x00\x00\x00\x00'\
    b'\x00\x00\x00\x00\x00\x00\x00\x00\x00\x00\x00\x00\x00\x00\x00\x00'\
    b'\x00\x00\x00\x00\x00\x00\x00\x00\x00\x06\x7c\x0d\xfc\x1e\x1c\x38'\
    b'\x18\x60\x30\xc0\x61\x80\xc3\x01\x86\x03\x0c\x06\x18\x0c\x30\x18'\
    b'\x60\x30\xc0\x60\x00\x00\x00\x00\x00\x00\x00\x00\x00\x00\x00\x00'\
    b'\x00\x00\x00\x00\x00\x00\x00\x00\x00\x00\x00\x00\x00\x00\x0f\xc0'\
    b'\x7f\xc1\xc1\xc3\x01\x8c\x01\x98\x03\x30\x06\x60\x0c\xc0\x19\x80'\
    b'\x71\x80\xc3\x83\x83\xfe\x03\xf0\x00\x00\x00\x00\x00\x00\x00\x00'\
    b'\x00\x00\x00\x00\x00\x00\x00\x00\x00\x00\x00\x00\x00\x00\x00\x00'\
    b'\x00\x00\x06\x7c\x0f\xfc\x1e\x1c\x38\x18\x60\x18\xc0\x31\x80\x63'\
    b'\x00\xc6\x01\x8c\x03\x1c\x0c\x3c\x38\x7f\xe0\xcf\x01\x80\x03\x00'\
    b'\x06\x00\x0c\x00\x18\x00\x00\x00\x00\x00\x00\x00\x00\x00\x00\x00'\
    b'\x00\x00\x00\x00\x00\x00\x00\x1f\x30\x7f\xe1\xc3\xc3\x03\x8c\x03'\
    b'\x18\x06\x30\x0c\x60\x18\xc0\x31\x80\x61\x81\xc3\x87\x83\xff\x03'\
    b'\xe6\x00\x0c\x00\x18\x00\x30\x00\x60\x00\xc0\x00\x00\x00\x00\x00'\
    b'\x00\x00\x00\x00\x01\xbc\xfe\x70\x38\x18\x0c\x06\x03\x01\x80\xc0'\
    b'\x60\x30\x18\x0c\x00\x00\x00\x00\x00\x00\x00\x00\x00\x00\x00\x00'\
    b'\x00\x00\x00\x00\x00\x00\x00\x00\x00\x00\x7f\x03\xfe\x1c\x1c\x60'\
    b'\x71\xc0\x07\xf8\x07\xf8\x07\xf0\x01\xe0\x01\x9c\x06\x78\x30\xff'\
    b'\xc0\xfc\x00\x00\x00\x00\x00\x00\x00\x00\x00\x00\x00\x00\x00\x10'\
    b'\x30\x30\x30\x30\xfc\xfc\x30\x30\x30\x30\x30\x30\x30\x30\x30\x30'\
    b'\x3e\x1e\x00\x00\x00\x00\x00\x00\x00\x00\x00\x00\x00\x00\x00\x00'\
    b'\x00\x00\x00\x00\x00\x00\x00\x00\x60\x30\xc0\x61\x80\xc3\x01\x86'\
    b'\x03\x0c\x06\x18\x0c\x30\x18\x60\x30\xc0\x61\x81\xc3\x87\x83\xff'\
    b'\x03\xe6\x00\x00\x00\x00\x00\x00\x00\x00\x00\x00\x00\x00\x00\x00'\
    b'\x00\x00\x00\x00\x00\x00\x00\x00\x00\x00\x00\x38\x06\x70\x31\xc0'\
    b'\xc7\x03\x0c\x18\x38\x60\xe3\x81\x8c\x07\x70\x0d\x80\x36\x00\xf8'\
    b'\x01\xc0\x07\x00\x00\x00\x00\x00\x00\x00\x00\x00\x00\x00\x00\x00'\
    b'\x00\x00\x00\x00\x00\x00\x00\x00\x00\x00\x00\x00\x00\x00\x00\x00'\
    b'\x00\x00\x00\xc0\x60\x66\x06\x06\x60\xf0\xc6\x0f\x0c\x30\xf0\xc3'\
    b'\x19\x88\x31\x99\x81\x99\x98\x19\x19\x81\xb0\xf0\x0f\x0f\x00\xf0'\
    b'\xf0\x0e\x06\x00\x60\x60\x00\x00\x00\x00\x00\x00\x00\x00\x00\x00'\
    b'\x00\x00\x00\x00\x00\x00\x00\x00\x00\x00\x00\x00\x00\x00\x00\x00'\
    b'\x00\x00\x1c\x0e\x38\x70\x61\x81\xce\x03\xf0\x07\x80\x1c\x00\x78'\
    b'\x03\xf0\x0c\xc0\x73\x81\x86\x0e\x1c\x70\x38\x00\x00\x00\x00\x00'\
    b'\x00\x00\x00\x00\x00\x00\x00\x00\x00\x00\x00\x00\x00\x00\x00\x00'\
    b'\x00\x00\x00\x18\x06\x30\x30\xc0\xc3\x03\x06\x18\x18\x60\x61\x80'\
    b'\xcc\x03\x30\x0c\xc0\x1e\x00\x78\x00\xc0\x03\x00\x0c\x00\x60\x01'\
    b'\x80\x3c\x00\xe0\x00\x00\x00\x00\x00\x00\x00\x00\x00\x00\x00\x00'\
    b'\x00\x00\x00\x00\x1f\xfe\x7f\xf8\x01\xe0\x07\x00\x38\x01\xc0\x0e'\
    b'\x00\x70\x03\x80\x1c\x00\xe0\x07\x80\x1f\xfe\x7f\xf8\x00\x00\x00'\
    b'\x00\x00\x00\x00\x00\x00\x00\x00\x00\x00\x00\x00\x00\x00\x00\x1c'\
    b'\x00\x07\x80\x03\xe0\x00\xdc\x00\x33\x00\x1c\xc0\x06\x38\x03\x86'\
    b'\x00\xe1\xc0\x30\x70\x1c\x0c\x07\xff\x81\xff\xe0\xff\xfc\x38\x07'\
    b'\x1c\x00\xe7\x00\x39\x80\x0e\xe0\x01\xc0\x00\x00\x00\x00\x00\x00'\
    b'\x00\x00\x00\x00\x00\x00\x00\x00\x00\x00\x00\x00\x00\x03\xff\xc0'\
    b'\xff\xfc\x3f\xff\x0e\x01\xe3\x80\x38\xe0\x0e\x38\x07\x0f\xff\xc3'\
    b'\xff\xe0\xff\xfc\x38\x0f\x8e\x00\xe3\x80\x38\xe0\x0e\x38\x03\x8e'\
    b'\x01\xe3\xff\xf0\xff\xf8\x3f\xf8\x00\x00\x00\x00\x00\x00\x00\x00'\
    b'\x00\x00\x00\x00\x00\x00\x00\x00\x00\x00\x00\x00\x00\x00\x1f\xc0'\
    b'\x07\xff\x00\xff\xf8\x1f\x03\xc3\xc0\x1e\x38\x00\xe7\x80\x00\x70'\
    b'\x00\x07\x00\x00\x70\x00\x07\x00\x00\x70\x00\x07\x80\x0c\x38\x00'\
    b'\xe3\xc0\x1c\x1f\x07\xc0\xff\xf8\x07\xff\x00\x1f\xc0\x00\x00\x00'\
    b'\x00\x00\x00\x00\x00\x00\x00\x00\x00\x00\x00\x00\x00\x00\x00\x00'\
    b'\x00\x00\x00\x03\xff\xc0\x3f\xff\x03\xff\xf8\x38\x07\xc3\x80\x3c'\
    b'\x38\x01\xc3\x80\x0e\x38\x00\xe3\x80\x0e\x38\x00\xe3\x80\x0e\x38'\
    b'\x00\xe3\x80\x0e\x38\x01\xc3\x80\x3c\x38\x07\x83\xff\xf8\x3f\xff'\
    b'\x03\xff\xc0\x00\x00\x00\x00\x00\x00\x00\x00\x00\x00\x00\x00\x00'\
    b'\x00\x00\x00\x00\x00\x00\x00\x00\x03\xff\xf8\xff\xfe\x3f\xff\x8e'\
    b'\x00\x03\x80\x00\xe0\x00\x38\x00\x0f\xff\x83\xff\xe0\xff\xf8\x38'\
    b'\x00\x0e\x00\x03\x80\x00\xe0\x00\x38\x00\x0e\x00\x03\xff\xf8\xff'\
    b'\xfe\x3f\xff\x80\x00\x00\x00\x00\x00\x00\x00\x00\x00\x00\x00\x00'\
    b'\x00\x00\x00\x00\x00\x00\x00\x3f\xff\x1f\xff\x8f\xff\xc7\x00\x03'\
    b'\x80\x01\xc0\x00\xe0\x00\x70\x00\x3f\xf8\x1f\xfc\x0f\xfe\x07\x00'\
    b'\x03\x80\x01\xc0\x00\xe0\x00\x70\x00\x38\x00\x1c\x00\x0e\x00\x00'\
    b'\x00\x00\x00\x00\x00\x00\x00\x00\x00\x00\x00\x00\x00\x00\x00\x00'\
    b'\x00\x00\x00\x00\x00\x1f\xc0\x03\xff\xc0\x3f\xff\x03\xe0\x78\x3c'\
    b'\x00\xe1\xc0\x03\x1e\x00\x00\xe0\x00\x07\x00\x00\x38\x0f\xf1\xc0'\
    b'\x7f\x8e\x03\xfc\x78\x00\xe1\xc0\x07\x0f\x00\x38\x3e\x07\xc0\xff'\
    b'\xfc\x03\xff\xc0\x07\xf0\x00\x00\x00\x00\x00\x00\x00\x00\x00\x00'\
    b'\x00\x00\x00\x00\x00\x00\x00\x00\x00\x00\x00\x00\x00\x03\x80\x1c'\
    b'\x38\x01\xc3\x80\x1c\x38\x01\xc3\x80\x1c\x38\x01\xc3\x80\x1c\x3f'\
    b'\xff\xc3\xff\xfc\x3f\xff\xc3\x80\x1c\x38\x01\xc3\x80\x1c\x38\x01'\
    b'\xc3\x80\x1c\x38\x01\xc3\x80\x1c\x38\x01\xc3\x80\x1c\x00\x00\x00'\
    b'\x00\x00\x00\x00\x00\x00\x00\x00\x00\x00\x00\x00\x00\x01\xc1\xc1'\
    b'\xc1\xc1\xc1\xc1\xc1\xc1\xc1\xc1\xc1\xc1\xc1\xc1\xc1\xc1\xc1\xc1'\
    b'\xc0\x00\x00\x00\x00\x00\x00\x00\x00\x00\x00\x00\x00\x07\x00\x1c'\
    b'\x00\x70\x01\xc0\x07\x00\x1c\x00\x70\x01\xc0\x07\x00\x1c\x00\x70'\
    b'\x01\xc0\x07\x0c\x1c\x30\x70\xe3\xc3\xfe\x07\xf8\x0f\x80\x00\x00'\
    b'\x00\x00\x00\x00\x00\x00\x00\x00\x00\x00\x00\x00\x00\x00\x00\x03'\
    b'\x80\x38\xe0\x1c\x38\x0e\x0e\x07\x03\x83\x80\xe1\xc0\x38\xe0\x0e'\
    b'\x70\x03\xbc\x00\xff\x80\x3e\x70\x0f\x0e\x03\x83\x80\xe0\x70\x38'\
    b'\x0e\x0e\x03\x83\x80\x70\xe0\x0e\x38\x03\xc0\x00\x00\x00\x00\x00'\
    b'\x00\x00\x00\x00\x00\x00\x00\x00\x00\x00\x00\x00\x00\x38\x00\x70'\
    b'\x00\xe0\x01\xc0\x03\x80\x07\x00\x0e\x00\x1c\x00\x38\x00\x70\x00'\
    b'\xe0\x01\xc0\x03\x80\x07\x00\x0e\x00\x1c\x00\x3f\xfc\x7f\xf8\xff'\
    b'\xf0\x00\x00\x00\x00\x00\x00\x00\x00\x00\x00\x00\x00\x00\x00\x00'\
    b'\x00\x00\x00\x00\x00\x38\x00\x70\xf0\x03\xc3\xc0\x0f\x0f\x00\x3c'\
    b'\x36\x01\xb0\xd8\x06\xc3\x60\x1b\x0c\xc0\xcc\x33\x03\x30\xce\x1c'\
    b'\xc3\x18\x63\x0c\x61\x8c\x30\xce\x30\xc3\x30\xc3\x0e\xc3\x0c\x1e'\
    b'\x0c\x30\x78\x30\xc1\xe0\xc3\x03\x03\x00\x00\x00\x00\x00\x00\x00'\
    b'\x00\x00\x00\x00\x00\x00\x00\x00\x00\x00\x00\x00\x00\x00\x00\x00'\
    b'\x00\x30\x00\xc3\x80\x0c\x3c\x00\xc3\xe0\x0c\x3f\x00\xc3\x70\x0c'\
    b'\x33\x80\xc3\x1c\x0c\x30\xe0\xc3\x0f\x0c\x30\x70\xc3\x03\x8c\x30'\
    b'\x1c\xc3\x00\xec\x30\x0f\xc3\x00\x7c\x30\x03\xc3\x00\x1c\x30\x00'\
    b'\xc0\x00\x00\x00\x00\x00\x00\x00\x00\x00\x00\x00\x00\x00\x00\x00'\
    b'\x00\x00\x00\x00\x00\x00\x00\x00\x1f\x80\x03\xff\x80\x3f\xfe\x03'\
    b'\xe0\xf8\x3c\x01\xe1\xc0\x07\x1e\x00\x3c\xe0\x00\xe7\x00\x07\x38'\
    b'\x00\x39\xc0\x01\xce\x00\x0e\x78\x00\xf1\xc0\x07\x0f\x00\x78\x3e'\
    b'\x0f\x80\xff\xf8\x03\xff\x80\x03\xe0\x00\x00\x00\x00\x00\x00\x00'\
    b'\x00\x00\x00\x00\x00\x00\x00\x00\x00\x00\x00\x00\x00\x00\x00\x03'\
    b'\xff\xc0\xff\xf8\x3f\xff\x0e\x01\xe3\x80\x38\xe0\x0e\x38\x03\x8e'\
    b'\x01\xe3\xff\xf0\xff\xf8\x3f\xf8\x0e\x00\x03\x80\x00\xe0\x00\x38'\
    b'\x00\x0e\x00\x03\x80\x00\xe0\x00\x38\x00\x00\x00\x00\x00\x00\x00'\
    b'\x00\x00\x00\x00\x00\x00\x00\x00\x00\x00\x00\x00\x00\x00\x00\x00'\
    b'\x01\xfc\x00\x3f\xf8\x03\xff\xe0\x3e\x0f\x83\xc0\x1e\x1c\x00\x71'\
    b'\xe0\x01\xce\x00\x0e\x70\x00\x73\x80\x03\x9c\x00\x1c\xe0\x00\xe7'\
    b'\x80\x8f\x1c\x07\x70\xf0\x1f\x83\xe0\x78\x0f\xff\x80\x3f\xfe\x00'\
    b'\x7f\x3c\x00\x00\xe0\x00\x00\x00\x00\x00\x00\x00\x00\x00\x00\x00'\
    b'\x00\x00\x00\x00\x00\x00\x00\x00\x00\x3f\xfe\x03\xff\xf0\x3f\xff'\
    b'\x83\x80\x3c\x38\x01\xc3\x80\x1c\x38\x01\xc3\x80\x3c\x3f\xff\x83'\
    b'\xff\xf0\x3f\xfc\x03\x81\xc0\x38\x0e\x03\x80\x70\x38\x03\x83\x80'\
    b'\x3c\x38\x01\xc3\x80\x0e\x38\x00\x70\x00\x00\x00\x00\x00\x00\x00'\
    b'\x00\x00\x00\x00\x00\x00\x00\x00\x00\x00\x00\x00\x00\x00\x03\xf0'\
    b'\x03\xff\x01\xff\xe0\xe0\x3c\x30\x03\x0c\x00\x03\xc0\x00\x7f\x80'\
    b'\x0f\xfc\x00\x7f\x80\x01\xf0\x00\x0e\x00\x01\x8c\x00\x63\x80\x38'\
    b'\x78\x1c\x1f\xff\x03\xff\x80\x3f\x80\x00\x00\x00\x00\x00\x00\x00'\
    b'\x00\x00\x00\x00\x00\x00\x00\x00\x00\x00\x00\x00\x03\xff\xe1\xff'\
    b'\xf0\xff\xf8\x03\x80\x01\xc0\x00\xe0\x00\x70\x00\x38\x00\x1c\x00'\
    b'\x0e\x00\x07\x00\x03\x80\x01\xc0\x00\xe0\x00\x70\x00\x38\x00\x1c'\
    b'\x00\x0e\x00\x07\x00\x00\x00\x00\x00\x00\x00\x00\x00\x00\x00\x00'\
    b'\x00\x00\x00\x00\x00\x00\x00\x00\x00\x03\x80\x1c\x38\x01\xc3\x80'\
    b'\x1c\x38\x01\xc3\x80\x1c\x38\x01\xc3\x80\x1c\x38\x01\xc3\x80\x1c'\
    b'\x38\x01\xc3\x80\x1c\x38\x01\xc3\x80\x1c\x38\x01\xc3\xc0\x3c\x1e'\
    b'\x07\x81\xff\xf8\x0f\xfe\x00\x3f\xc0\x00\x00\x00\x00\x00\x00\x00'\
    b'\x00\x00\x00\x00\x00\x00\x00\x00\x00\x00\x00\x00\x00\x00\x0e\x00'\
    b'\x1d\xc0\x0e\x70\x03\x9c\x00\xe3\x00\x70\xe0\x1c\x38\x0e\x06\x03'\
    b'\x81\xc0\xc0\x70\x70\x0c\x1c\x03\x8e\x00\x63\x80\x18\xc0\x07\x70'\
    b'\x00\xd8\x00\x36\x00\x0f\x80\x01\xc0\x00\x00\x00\x00\x00\x00\x00'\
    b'\x00\x00\x00\x00\x00\x00\x00\x00\x00\x00\x00\x00\x00\x00\x00\x00'\
    b'\x00\xe0\x1c\x03\xf0\x0e\x01\xdc\x0d\x81\xce\x06\xc0\xe7\x03\x60'\
    b'\x73\x83\xb8\x38\xc1\x8c\x18\x70\xc6\x1c\x38\xe3\x8e\x1c\x71\xc7'\
    b'\x06\x30\x63\x03\x98\x33\x81\xdc\x1d\xc0\x6c\x06\xc0\x36\x03\x60'\
    b'\x1b\x01\xb0\x0f\x80\xf8\x03\x80\x38\x01\xc0\x1c\x00\x00\x00\x00'\
    b'\x00\x00\x00\x00\x00\x00\x00\x00\x00\x00\x00\x00\x00\x00\x00\x00'\
    b'\x00\x00\x00\x00\x00\x07\x00\x0c\x70\x03\x07\x00\xc0\x70\x30\x0f'\
    b'\x0c\x00\xe3\x80\x0e\xe0\x00\xf8\x00\x0e\x00\x01\xc0\x00\x7c\x00'\
    b'\x1d\xc0\x03\x1c\x00\xe1\xc0\x38\x38\x0e\x03\x81\xc0\x38\x70\x03'\
    b'\x9c\x00\x38\x00\x00\x00\x00\x00\x00\x00\x00\x00\x00\x00\x00\x00'\
    b'\x00\x00\x00\x00\x00\x00\x00\x0e\x00\x39\xc0\x1c\x38\x0e\x0e\x03'\
    b'\x81\xc1\xc0\x38\x70\x0e\x38\x01\xdc\x00\x77\x00\x0f\x80\x01\xc0'\
    b'\x00\x70\x00\x1c\x00\x07\x00\x01\xc0\x00\x70\x00\x1c\x00\x07\x00'\
    b'\x01\xc0\x00\x00\x00\x00\x00\x00\x00\x00\x00\x00\x00\x00\x00\x00'\
    b'\x00\x00\x00\x00\x00\x00\x3f\xff\x1f\xff\x8f\xff\xc0\x01\xe0\x01'\
    b'\xe0\x00\xe0\x00\xe0\x00\xe0\x00\xe0\x00\xe0\x00\xe0\x00\xe0\x00'\
    b'\xe0\x00\xe0\x00\xe0\x00\xe0\x00\x7f\xff\x3f\xff\x9f\xff\xc0\x00'\
    b'\x00\x00\x00\x00\x00\x00\x00\x00\x00\x00\x00\x00\x00\x00\x00\x00'\
    b'\x00\x00\x00\x00\x78\x07\xf8\x38\x70\xc0\xc7\x03\x18\x06\x60\x19'\
    b'\x80\x66\x01\x98\x06\x60\x19\x80\x67\x03\x0c\x0c\x38\x70\x7f\x80'\
    b'\x78\x00\x00\x00\x00\x00\x00\x00\x00\x00\x00\x00\x00\x00\x00\x00'\
    b'\x00\x00\x00\x00\x00\x30\x03\xc0\x1f\x00\xec\x01\x30\x00\xc0\x03'\
    b'\x00\x0c\x00\x30\x00\xc0\x03\x00\x0c\x00\x30\x00\xc0\x03\x00\x0c'\
    b'\x00\x30\x00\x00\x00\x00\x00\x00\x00\x00\x00\x00\x00\x00\x00\x00'\
    b'\x00\x00\x00\x00\x00\x00\x78\x03\xf8\x1c\x60\xe0\xc1\x03\x00\x0c'\
    b'\x00\x30\x01\x80\x0c\x00\x60\x03\x80\x18\x00\xc0\x03\x00\x18\x00'\
    b'\x7f\xc1\xff\x00\x00\x00\x00\x00\x00\x00\x00\x00\x00\x00\x00\x00'\
    b'\x00\x00\x00\x00\x00\x00\x03\xfe\x0f\xf8\x00\xc0\x06\x00\x30\x00'\
    b'\x80\x07\x80\x3f\x80\xc6\x00\x0c\x00\x30\x00\xc0\x03\x08\x1c\x78'\
    b'\xe0\xff\x01\xf0\x00\x00\x00\x00\x00\x00\x00\x00\x00\x00\x00\x00'\
    b'\x00\x00\x00\x00\x00\x00\x00\x00\x1e\x00\xf8\x07\x60\x19\x80\xc6'\
    b'\x03\x18\x18\x60\x61\x81\x86\x0c\x18\x7f\xf9\xff\xe0\x06\x00\x18'\
    b'\x00\x60\x01\x80\x06\x00\x00\x00\x00\x00\x00\x00\x00\x00\x00\x00'\
    b'\x00\x00\x00\x00\x00\x00\x00\x00\x00\xfe\x03\xf8\x18\x00\x60\x01'\
    b'\x80\x07\xe0\x3f\xe0\xe3\x80\x07\x00\x0c\x00\x30\x00\xc0\x03\x04'\
    b'\x1c\x38\x60\x7f\x00\xf8\x00\x00\x00\x00\x00\x00\x00\x00\x00\x00'\
    b'\x00\x00\x00\x00\x00\x00\x00\x00\x00\x00\x0f\x00\xfc\x0f\x00\x70'\
    b'\x03\x00\x0c\x00\x6f\xc1\xff\x87\x87\x1c\x0e\x60\x19\x80\x66\x01'\
    b'\x8c\x0e\x38\x70\x7f\x80\xfc\x00\x00\x00\x00\x00\x00\x00\x00\x00'\
    b'\x00\x00\x00\x00\x00\x00\x00\x00\x00\x00\x03\xff\x0f\xfc\x00\x30'\
    b'\x01\x80\x06\x00\x30\x00\xc0\x06\x00\x18\x00\xc0\x03\x00\x18\x00'\
    b'\x60\x01\x80\x0c\x00\x30\x00\xc0\x00\x00\x00\x00\x00\x00\x00\x00'\
    b'\x00\x00\x00\x00\x00\x00\x00\x00\x00\x00\x00\x00\xf8\x07\xf0\x38'\
    b'\xe0\xc1\x83\x06\x0c\x18\x18\xc0\x7f\x01\xfc\x0e\x38\x70\x31\x80'\
    b'\xc6\x03\x18\x0c\x38\xe0\xff\x80\xf8\x00\x00\x00\x00\x00\x00\x00'\
    b'\x00\x00\x00\x00\x00\x00\x00\x00\x00\x00\x00\x00\x00\xf8\x0f\xf0'\
    b'\x38\xe1\xc1\x86\x03\x18\x0c\x60\x31\xc1\xc3\x8f\x0f\xfc\x0f\xb0'\
    b'\x00\x80\x06\x00\x30\x07\x80\xfc\x03\xc0\x00\x00\x00\x00\x00\x00'\
    b'\x00\x00\x00\x00\x00\x00\x00\x00\x00\x18\x18\x18\x18\x18\x18\x18'\
    b'\x18\x18\x18\x18\x18\x00\x00\x18\x18\x18\x00\x00\x00\x00\x00\x00'\
    b'\x00\x00\x00\x00\x00\x00\x00\x00\x00\x00\x44\x04\x40\x44\x04\x40'\
    b'\x44\x7f\xf0\x88\x08\x80\x88\x08\x8f\xfe\x11\x01\x10\x33\x02\x20'\
    b'\x22\x00\x00\x00\x00\x00\x00\x00\x00\x00\x00\x00\x00\x00\x00\x1f'\
    b'\x03\x18\x60\xc4\x04\x40\x44\x04\x60\xc3\x18\x1f\x00\x00\x00\x00'\
    b'\x00\x00\x00\x00\x00\x00\x00\x00\x00\x00\x00\x00\x00\x00\x00\x00'\
    b'\x00\x00\x00\x00\x00\x00\x00\x0c\x00\x60\x03\x00\x0c\x00\x30\x00'\
    b'\xc0\x03\x00\x0c\x00\x30\x00\xc0\x03\x00\x1c\x00\xc0\x01\x80\x03'\
    b'\x00\x0c\x00\x30\x00\xc0\x03\x00\x0c\x00\x30\x00\xc0\x03\x00\x0c'\
    b'\x00\x18\x00\x30\x00\x00\x00\x00\x00\x00\x00\x00\x00\x00\x00\x00'\
    b'\x00\x00\x00\x00\x00\x00\x00\x00\x00\x00\x00\x00\x00\x00\x00\x00'\
    b'\x00\x00\x00\x00\x60\x00\xc0\x01\x80\x06\x00\x18\x00\x60\x01\x80'\
    b'\x06\x00\x18\x00\x60\x01\x80\x06\x00\x0c\x00\x18\x00\xc0\x06\x00'\
    b'\x18\x00\x60\x01\x80\x06\x00\x18\x00\x60\x01\x80\x06\x00\x30\x01'\
    b'\x80\x00\x00\x00\x00\x00\x00\x00\x01\x00\x04\x00\x7c\x07\xfc\x39'\
    b'\x38\xc4\x63\x10\x0c\x40\x1d\x00\x3c\x00\x3c\x00\x7c\x01\x38\x04'\
    b'\x34\x10\xd8\x43\x39\x3c\x7f\xe0\x7e\x00\x40\x01\x00\x00\x00\x00'\
    b'\x00\x00\x00\x00\x00\x00\x00\x00\x00\x00\x00\x00\x00\x00\x00\x00'\
    b'\x00\x06\x01\xe0\x18\x0f\xc0\xc0\x73\x82\x01\x86\x18\x06\x18\xc0'\
    b'\x1c\xe2\x00\x3f\x18\x00\x78\xc0\x00\x03\x00\x00\x18\xf0\x00\x47'\
    b'\xe0\x03\x39\xc0\x18\xc3\x00\x43\x0c\x03\x0e\x70\x18\x1f\x80\x60'\
    b'\x3c\x00\x00\x00\x00\x00\x00\x00\x00\x00\x00\x00\x00\x00\x00\x00'\
    b'\x00\x00\x00\x00\x00\x00\x00\x00\x00\x00\x00\x00\x00\x00\x78\x00'\
    b'\x18\x80\x06\x10\x00\xc2\x00\x18\x40\x03\x90\x00\x34\xf8\x07\x06'\
    b'\x03\x60\x81\x8e\x20\x30\xc4\x0c\x1d\x01\x81\xc0\x30\x38\x07\x03'\
    b'\xc2\x71\xbf\x87\xc1\xe0\x00\x00\x00\x00\x00\x00\x00\x00\x00\x00'\
    b'\x00\x00\x00\x00\x00\x00\x00\x00\xc1\xc1\x81\x83\x03\x00\x00\x00'\
    b'\x00\x00\x00\x00\x00\x00\x00\x00\x00\x00\x00\x00\x00\x00\x00\x00'\
    b'\x00\x00\x00\x00\x00\xc0\x40\x40\x60\x20\x10\x10\x08\x04\x02\x01'\
    b'\x00\x80\x40\x20\x08\x04\x03\x00\x80\x20\x18\x00\x00\x00\x00\x00'\
    b'\x00\x00\x00\x00\xc0\x20\x08\x06\x01\x00\x80\x20\x10\x08\x04\x02'\
    b'\x01\x00\x80\x40\x40\x20\x30\x10\x10\x18\x00\x00\x00\x18\x00\x30'\
    b'\x00\x60\x1c\x8e\x1d\x78\x0f\xc0\x0f\x00\x7f\x83\xd7\xc6\x23\x80'\
    b'\x60\x00\xc0\x01\x80\x00\x00\x00\x00\x00\x00\x00\x00\x00\x00\x00'\
    b'\x00\x00\x00\x00\x00\x00\x00\x00\x00\x00\x00\x00\x00\x00\x00\x00'\
    b'\x00\x00\x00\x00\x00\x00\x00\x00\x00\x00\x00\x00\x03\x01\x80\xc0'\
    b'\x00\x00\x00\x00\x00\x00\x01\x81\xc0\xc0\x60\x60\x30\x00\x00\x00'\
    b'\x00\x00\x00\x00\x00\x00\x00\x00\x00\x00\x00\x00\x00\x00\x00\x00'\
    b'\x00\x00\x00\x00\x00\x00\x00\x18\x00\x3c\x00\x78\x01\xf0\x03\xc0'\
    b'\x07\x80\x03\x80\x00\xf0\x00\x1e\x00\x03\xc0\x00\x7c\x00\x07\x00'\
    b'\x00\x80\x00\x00\x00\x00\x00\x00\x00\x00\x00\x00\x00\x00\x00\x00'\
    b'\x00\x00\x00\x00\x00\x00\x00\x00\x00\x00\x00\x00\x00\x00\x00\x00'\
    b'\x00\x00\x00\x00\x00\x00\x00\x00\x00\x00\x00\x01\xff\xf0\x7f\xfc'\
    b'\x00\x00\x00\x00\x01\xff\xf0\x7f\xfc\x00\x00\x00\x00\x00\x00\x00'\
    b'\x00\x00\x00\x00\x00\x00\x00\x00\x00\x00\x00\x00\x00\x00\x00\x00'\
    b'\x00\x00\x00\x00\x00\x00\x00\x00\x00\x00\x00\x00\x00\x00\x00\x00'\
    b'\x0c\x00\x07\x80\x00\xf0\x00\x1e\x00\x03\xc0\x00\x7c\x00\x06\x00'\
    b'\x1f\x00\x3c\x00\x78\x00\xf0\x01\xe0\x00\x80\x00\x00\x00\x00\x00'\
    b'\x00\x00\x00\x00\x00\x00\x00\x00\x00\x00\x00\x00\x00\x00\x00\x00'\
    b'\x00\x00\x00\x00\x00\x3f\xc0\x00\x3f\xff\x00\x0f\x80\xf0\x03\x80'\
    b'\x07\x00\xe0\x00\x30\x38\x1e\x67\x06\x0f\xec\x61\x83\x87\x06\x30'\
    b'\xe0\xe0\xcc\x18\x0c\x19\x87\x01\x83\x30\xc0\x30\x66\x18\x04\x1c'\
    b'\xc3\x01\x83\x18\x60\x30\xe3\x0e\x0e\x38\x30\xc3\xce\x06\x1f\xbf'\
    b'\x80\xe1\xe3\xc3\x0e\x00\x00\xc0\xf0\x00\x70\x0f\x80\x3c\x00\x7f'\
    b'\xfe\x00\x03\xff\x00\x00\x00\x00\x00\x00\x00\x00\x00\x00\x00\x00'\
    b'\x44\x04\x40\x44\x04\x40\x44\x7f\xf0\x88\x08\x80\x88\x08\x8f\xfe'\
    b'\x11\x01\x10\x33\x02\x20\x22\x00\x00\x00\x00\x00\x00\x00\x00\x00'\
    b'\x00\x00\x00\x00\x00\x00\x00\x00\x00\x00\x00\x00\x00\x00\x00\x00'\
    b'\x00\x00\x00\x00\x00\x00\x00\x00\x00\x1e\x02\x7f\x87\x61\xfe\xc0'\
    b'\x78\x80\x00\x00\x00\x00\x00\x00\x00\x00\x00\x00\x00\x00\x00\x00'\
    b'\x00\x00\x00\x00\x00\x00\x00\x00\x00\x00\x00\x00\x00\x00\x00\x00'\
    b'\x00\x00\x40\x0a\x00\xa0\x11\x03\x18\x20\x84\x04\x40\x48\x02\x00'\
    b'\x00\x00\x00\x00\x00\x00\x00\x00\x00\x00\x00\x00\x00\x00\x00\x00'\
    b'\x00\x00\x00\x00\x00\x00\x00\x00\x01\x00\x04\x00\x7c\x07\xfc\x39'\
    b'\x38\xc4\x63\x10\x0c\x40\x1d\x00\x3c\x00\x3c\x00\x7c\x01\x38\x04'\
    b'\x34\x10\xd8\x43\x39\x3c\x7f\xe0\x7e\x00\x40\x01\x00\x00\x00\x00'\
    b'\x00\x00\x00\x00\x00\x00\x00\x00\x18\x18\x18\x18\x18\x18\x18\x18'\
    b'\x18\x18\x18\x18\x00\x00\x18\x18\x18\x00\x00\x00\x00\x00\x00\x00'\
    b'\x00\x00\x00\x00\x00\x3c\x0f\xc3\x9c\x61\x8c\x30\x06\x01\x80\x30'\
    b'\x0c\x01\x80\x60\x0c\x01\x80\x00\x00\x00\xc0\x18\x03\x00\x00\x00'\
    b'\x00\x00\x00\x00\x00\x00\x00\x00\x00\x00\x00\x00\x00\x00\x00\x00'\
    b'\x00\x00\x00\x00\x00\x00\x00\x00\x00\x01\x80\x00\x60\x00\x18\x00'\
    b'\x06\x00\x01\x80\x00\x60\x07\xff\xe1\xff\xf8\x01\x80\x00\x60\x00'\
    b'\x18\x00\x06\x00\x01\x80\x00\x60\x00\x00\x00\x00\x00\x00\x00\x00'\
    b'\x00\x00\x00\x00\x00\x00\x00\x00\x00\x00\x00\x00\x00\x00\x00\x00'\
    b'\x00\x00\x00\x00\x00\x00\x00\xc1\xc1\x81\x83\x03\x00\x00\x00\x00'\
    b'\x00\x00\x00\x00\x00\x00\x00\x00\x00\x00\x00\x00\x00\x07\xe7\xe0'\
    b'\x00\x00\x00\x00\x00\x00\x00\x00\x00\x00\x00\x00\x00\x00\x00\x00'\
    b'\x00\x00\x00\x00\x00\x01\x81\x81\x80\x00\x00\x00\x00\x00\x00\x01'\
    b'\x81\x81\x80\x00\x00\x00\x00\x00\x00\x00\x00\x00\x00\x00\x00\x00'\
    b'\x00\x00\x00\x00\x00\x00\x00\x00\x00\x00\x00\x01\x81\x81\x80\x00'\
    b'\x00\x00\x00\x00\x00\x00\x00\x06\x00\x40\x04\x00\xc0\x08\x01\x80'\
    b'\x18\x01\x00\x30\x03\x00\x20\x06\x00\x40\x0c\x00\xc0\x08\x01\x80'\
    b'\x18\x01\x00\x30\x02\x00\x20\x06\x00\x00\x00\x00\x00\x00\x00\x00'\
    b'\x00\x00\x00\x00\x00\x00\x00\x00\x00\x00\x0c\x0f\x03\x07\xc0\xc0'\
    b'\x60\x60\x30\x18\x18\x0e\x0c\x0f\x86\x0e\xc6\x0c\x3f\x06\x1e\x03'\
    b'\x06\x01\x81\x80\xc0\x60\x60\x30\x30\x0c\x1f\x03\x07\x80\xc0\x00'\
    b'\x00\x00\x00\x00\x00\x00\x00\x00\x00\x00\x00\x00\x00\x00\x00\x00'\
    b'\x00\x00\x00\x00\x00\x1f\xe0\x1f\xf0\x00\x18\x00\x18\x00\x18\x00'\
    b'\x18\x00\x18\x00\x18\x00\x18\x00\x18\x00\x18\x00\x18\x00\x18\x00'\
    b'\x18\x00\x18\x3f\xfe\x3f\xfe\x00\x00\x00\x00\x00\x00\x00\x00\x00'\
    b'\x00\x00\x00\x00\x00\x00\x00\x00\x00\x00\x0f\xc0\xfc\x00\xc0\x0c'\
    b'\x00\xc0\x0c\x00\xc0\x0c\x00\xc0\x0c\x01\xc0\x3c\x07\xc0\xec\x1c'\
    b'\xc7\x8c\x60\xc0\x00\x00\x00\x00\x00\x00\x00\x00\x00\x00\x00\x00'\
    b'\x00\x00\x00\x00\x00\x07\xff\x9f\xfe\x00\xc0\x03\x00\x0c\x00\x30'\
    b'\x00\xc0\x03\x00\x0c\x00\x30\x00\xc0\x03\x00\x0c\x00\x30\x00\xc0'\
    b'\x03\x00\x0c\x00\x00\x00\x00\x00\x00\x00\x00\x00\x00\x00\x00\x00'\
    b'\x00\x00\x00\x00\x00\x00\x00\x00\x00\xff\xf8\x7f\xfc\x00\x06\x00'\
    b'\x03\x00\x01\x80\x00\xc1\x80\x60\xc0\x30\x60\x18\x30\x0c\x18\x06'\
    b'\x0c\x03\x06\x01\x83\x00\xc1\x80\x60\xc0\x30\x60\x18\x00\x00\x00'\
    b'\x00\x00\x00\x00\x00\x00\x00\x00\x00\x00\x00\x00\x00\x00\x00\x7e'\
    b'\x1f\x80\x60\x18\x06\x01\x80\x60\x18\x06\x01\x80\x60\x18\x06\x01'\
    b'\x80\x60\x18\x06\x00\x00\x00\x00\x00\x00\x00\x00\x00\x00\x00\x00'\
    b'\x00\x3f\xdf\xe1\x80\xc0\x60\x30\x18\x0c\x06\x03\x01\x80\xc0\x60'\
    b'\x30\x18\x0c\x06\x00\x00\x00\x00\x00\x00\x00\x00\x00\x00\x00\x00'\
    b'\x00\x00\x00\x00\x00\x00\x01\xff\xe0\xff\xf0\x18\x18\x0c\x0c\x06'\
    b'\x06\x03\x03\x01\x81\x80\xc0\xc0\x60\x60\x30\x30\x18\x18\x0c\x0c'\
    b'\x06\x06\x03\x03\x01\x81\x80\xc0\xc0\x60\x60\x00\x00\x00\x00\x00'\
    b'\x00\x00\x00\x00\x00\x00\x00\x00\x00\x00\x00\x00\x00\x00\x00\x00'\
    b'\x00\x00\x1e\x3c\x0f\x3f\x01\xb9\xc0\xd8\x60\x6c\x30\x36\x18\x1b'\
    b'\x0c\x0c\x06\x06\x03\x03\x01\x81\x80\xc0\xc0\x60\x60\x30\x38\x18'\
    b'\x1e\x1c\x07\xfc\x01\xfc\x00\x00\x00\x00\x00\x00\x00\x00\x00\x00'\
    b'\x00\x00\x00\x00\x00\x00\x00\x00\x03\xf0\xfc\x03\x00\xc0\x30\x0c'\
    b'\x03\x00\xc0\x00\x00\x00\x00\x00\x00\x00\x00\x00\x00\x00\x00\x00'\
    b'\x00\x00\x00\x00\x00\x00\x00\x00\x00\x00\x00\x00\x00\x00\x00\x00'\
    b'\x7f\xe0\x7f\xf0\x00\x38\x00\x18\x00\x18\x00\x18\x00\x18\x00\x18'\
    b'\x00\x18\x00\x18\x00\x18\x00\x18\x00\x18\x00\x18\x00\x38\x7f\xf0'\
    b'\x7f\xe0\x00\x00\x00\x00\x00\x00\x00\x00\x00\x00\x00\x00\x00\x00'\
    b'\x00\x00\x00\x00\x00\x00\x07\xfe\x1f\xf8\x00\x60\x01\x80\x06\x00'\
    b'\x18\x00\x60\x01\x80\x06\x00\x18\x00\x60\x01\x80\x06\x00\x18\x00'\
    b'\x60\x01\x80\x06\x00\x18\x00\x60\x01\x80\x06\x00\x00\x00\x00\x00'\
    b'\x00\x00\x00\x60\x00\x60\x00\x60\x00\x7f\xfc\x7f\xfc\x00\x0c\x00'\
    b'\x0c\x00\x0c\x00\x0c\x00\x0c\x00\x0c\x00\x1c\x00\x38\x00\x70\x00'\
    b'\xe0\x01\xc0\x03\x80\x03\x00\x03\x00\x03\x00\x00\x00\x00\x00\x00'\
    b'\x00\x00\x00\x00\x00\x00\x00\x00\x00\x00\x00\x00\x00\x00\x00\x00'\
    b'\x00\x01\xe3\xc0\xf7\xf0\x1e\x1c\x0e\x06\x07\x03\x03\x01\x81\x80'\
    b'\xc0\xc0\x60\x60\x30\x30\x18\x18\x0c\x0c\x06\x06\x03\x03\x01\x81'\
    b'\x80\xc0\xc7\xe0\x63\xf0\x00\x00\x00\x00\x00\x00\x00\x00\x00\x00'\
    b'\x00\x00\x00\x00\x00\x00\x00\x00\x00\x00\x00\x00\x00\x1f\xff\x8f'\
    b'\xff\xc1\x80\x60\xc0\x30\x60\x18\x30\x0c\x18\x06\x0c\x03\x06\x01'\
    b'\x83\x00\xc1\x80\x60\xc0\x30\x60\x18\x30\x0c\x18\x06\x0f\xff\x07'\
    b'\xff\x80\x00\x00\x00\x00\x00\x00\x00\x00\x00\x00\x00\x00\x00\x00'\
    b'\x00\x00\x00\x03\xe0\xf8\x06\x01\x80\x60\x18\x06\x01\x80\x60\x18'\
    b'\x06\x01\x80\x60\x18\x06\x1f\x87\xe0\x00\x00\x00\x00\x00\x00\x00'\
    b'\x00\x00\x00\x00\x00\x01\xf0\xf8\x0c\x06\x03\x01\x80\xc0\x60\x30'\
    b'\x18\x0c\x06\x03\x01\x80\xc0\x60\x30\x18\x0c\x06\x03\x00\x00\x00'\
    b'\x00\x00\x00\x00\x00\x00\x00\x00\x00\x00\x07\xff\x07\xff\x81\x81'\
    b'\x81\x81\x81\x81\x81\x81\x81\x81\x81\x81\x81\x81\x81\x81\x81\x81'\
    b'\x81\x81\x81\x81\x81\x81\x81\xc3\x80\xff\x00\x7c\x00\x00\x00\x00'\
    b'\x00\x00\x00\x00\x00\x00\x00\x00\x00\x00\x00\x00\x00\x00\x00\x00'\
    b'\x00\x00\x00\x1f\x1f\x0f\x8f\x80\xc0\xc0\x60\x60\x30\x30\x18\x18'\
    b'\x0c\x0c\x06\x06\x03\x03\x01\x81\x80\xc0\xc0\x60\x60\x30\x30\x18'\
    b'\x30\x0c\x38\x3f\xf8\x1f\xf0\x00\x00\x00\x00\x00\x00\x00\x00\x00'\
    b'\x00\x00\x00\x00\x00\x00\x00\x00\x00\x00\x00\x00\x00\x00\x3f\xf8'\
    b'\x3f\xf8\x30\x18\x30\x18\x30\x18\x30\x18\x30\x18\x30\x18\x3f\x18'\
    b'\x3f\x18\x00\x18\x00\x18\x00\x18\x00\x18\x00\x18\x3f\xf8\x3f\xf0'\
    b'\x00\x00\x00\x00\x00\x00\x00\x00\x00\x00\x00\x00\x00\x00\x00\x00'\
    b'\x00\x00\x00\x00\x00\x00\x3f\xf8\x3f\xf8\x30\x18\x30\x18\x30\x18'\
    b'\x30\x18\x30\x18\x30\x18\x30\x18\x3f\x18\x3f\x18\x00\x18\x00\x18'\
    b'\x00\x18\x00\x18\x00\x18\x00\x18\x00\x18\x00\x18\x00\x18\x00\x18'\
    b'\x00\x00\x00\x00\x00\x00\x00\x00\x00\x00\x00\x00\x00\x00\xf8\x7c'\
    b'\xf8\x7c\x18\x0c\x18\x0c\x18\x0c\x18\x18\x0c\x30\x06\x70\x03\xe0'\
    b'\x00\xe0\x00\x70\x00\x38\x00\x18\x00\x0c\x00\x0c\xff\xfc\xff\xfc'\
    b'\x00\x00\x00\x00\x00\x00\x00\x00\x00\x00\x00\x00\x00\x00\x00\x00'\
    b'\x00\x00\x00\x00\x00\x3e\x1f\x7c\x3e\x18\x0c\x30\x18\x60\x30\xc0'\
    b'\xc1\x83\x03\x1e\x07\xf0\x0f\x80\x18\x00\x30\x00\x60\x00\xc0\x01'\
    b'\x80\x03\x00\x06\x00\x0c\x00\x18\x00\x30\x00\x60\x00\x00\x00\x00'\
    b'\x00\x00\x00\x00\x00\x00\x00\x00\x00\x00\x07\xff\xc7\xff\xc0\x00'\
    b'\xc0\x00\xc0\x00\xc3\x00\xc3\x00\xc3\x00\xc3\x01\xc3\x03\x83\x07'\
    b'\x03\x0e\x03\x0c\x03\x18\x03\x18\x03\x18\x03\x18\x03\x00\x03\x00'\
    b'\x03\x00\x03\x00\x00\x00\x00\x00\x00\x00\x00\x00\x00\x00\x00\x00'\
    b'\x00\x7f\xf1\xff\xc0\x03\x00\x0c\x00\x30\x00\xc0\x03\x00\x0c\x00'\
    b'\x30\x00\xc0\x03\x00\x0c\x00\x30\x00\xc0\x03\x00\x0c\x00\x30\x00'\
    b'\x00\x00\x00\x00\x00\x00\x00\x00\x00\x00\x00\x00\x00\x00\x00\x00'\
    b'\x00\x00\x00\x00\x00\x00\xf3\x1e\x1e\x63\xc3\x0c\x18\x61\x83\x0c'\
    b'\x30\x61\x86\x0c\x30\xc1\x86\x18\x30\xc3\x06\x18\x60\xc3\x0c\x18'\
    b'\x61\x83\x0c\x30\x61\x86\x0c\x30\xc1\x87\xff\xe0\x7f\xf8\x00\x00'\
    b'\x00\x00\x00\x00\x00\x00\x00\x00\x00\x00\x00\x00\x00\x00\x00\x00'\
    b'\x00\x00\x00\x00\x00\x00\x00\xff\xf0\x7f\xf8\x0c\x0c\x06\x06\x03'\
    b'\x03\x01\x81\x80\xc0\xc0\x60\x60\x30\x30\x18\x18\x0c\x0c\x06\x06'\
    b'\x03\x03\x01\x81\x80\xc0\xc1\xe0\x60\xf0\x30\x00\x00\x00\x00\x00'\
    b'\x00\x00\x00\x00\x00\x00'

WIDTHS = memoryview(_WIDTHS)
OFFSETS = memoryview(_OFFSETS)
BITMAPS = memoryview(_BITMAPS)
