sgbmzm/Halacha-T-S3/drivers/miriam40.py

# -*- coding: utf-8 -*-
# Converted from miriam.ttf using:
#     ./font2bitmap.py miriam.ttf -s 'abcdefghijklmnopqrstuvwxyzABCDEFGHIJKLMNOPQRSTUVWXYZ0123456789!#°{ }$%&'"'"'()*;<=>@#~^$!?+,-:./אבגדהוזחטיכךלמםנןסעפףצץקרשת' 40

MAP = (
    'abcdefghijklmnopqrstuvwxyzABCDEF'
    'GHIJKLMNOPQRSTUVWXYZ0123456789!#'
    '°{ }$%&\'()*;<=>@#~^$!?+,-:./אבג'
    'דהוזחטיכךלמםנןסעפףצץקרשת'
)

BPP = 1
HEIGHT = 37
MAX_WIDTH = 37
_WIDTHS = \
    b'\x14\x14\x12\x14\x14\x0a\x14\x14\x08\x0a\x12\x08\x1e\x14\x14\x14'\
    b'\x14\x0c\x12\x0a\x14\x12\x1a\x12\x12\x12\x18\x18\x1a\x1a\x18\x16'\
    b'\x1c\x1a\x0a\x12\x18\x14\x1e\x1a\x1c\x18\x1c\x1a\x18\x16\x1a\x18'\
    b'\x22\x18\x18\x16\x13\x13\x13\x13\x13\x13\x13\x13\x13\x13\x0b\x11'\
    b'\x0f\x13\x0b\x13\x13\x1d\x1a\x0b\x0c\x0c\x14\x0c\x16\x18\x16\x25'\
    b'\x11\x16\x0f\x13\x0b\x0e\x18\x0b\x0b\x0b\x0b\x0f\x17\x15\x11\x13'\
    b'\x17\x0d\x0c\x16\x16\x0d\x15\x13\x15\x16\x16\x0d\x0b\x15\x16\x15'\
    b'\x15\x15\x14\x15\x13\x19\x17'

OFFSET_WIDTH = 3
_OFFSETS = \
    b'\x00\x00\x00\x00\x02\xe4\x00\x05\xc8\x00\x08\x62\x00\x0b\x46\x00'\
    b'\x0e\x2a\x00\x0f\x9c\x00\x12\x80\x00\x15\x64\x00\x16\x8c\x00\x17'\
    b'\xfe\x00\x1a\x98\x00\x1b\xc0\x00\x20\x16\x00\x22\xfa\x00\x25\xde'\
    b'\x00\x28\xc2\x00\x2b\xa6\x00\x2d\x62\x00\x2f\xfc\x00\x31\x6e\x00'\
    b'\x34\x52\x00\x36\xec\x00\x3a\xae\x00\x3d\x48\x00\x3f\xe2\x00\x42'\
    b'\x7c\x00\x45\xf4\x00\x49\x6c\x00\x4d\x2e\x00\x50\xf0\x00\x54\x68'\
    b'\x00\x57\x96\x00\x5b\xa2\x00\x5f\x64\x00\x60\xd6\x00\x63\x70\x00'\
    b'\x66\xe8\x00\x69\xcc\x00\x6e\x22\x00\x71\xe4\x00\x75\xf0\x00\x79'\
    b'\x68\x00\x7d\x74\x00\x81\x36\x00\x84\xae\x00\x87\xdc\x00\x8b\x9e'\
    b'\x00\x8f\x16\x00\x94\x00\x00\x97\x78\x00\x9a\xf0\x00\x9e\x1e\x00'\
    b'\xa0\xdd\x00\xa3\x9c\x00\xa6\x5b\x00\xa9\x1a\x00\xab\xd9\x00\xae'\
    b'\x98\x00\xb1\x57\x00\xb4\x16\x00\xb6\xd5\x00\xb9\x94\x00\xbb\x2b'\
    b'\x00\xbd\xa0\x00\xbf\xcb\x00\xc2\x8a\x00\xc4\x21\x00\xc6\xe0\x00'\
    b'\xc9\x9f\x00\xcd\xd0\x00\xd1\x92\x00\xd3\x29\x00\xd4\xe5\x00\xd6'\
    b'\xa1\x00\xd9\x85\x00\xdb\x41\x00\xde\x6f\x00\xe1\xe7\x00\xe5\x15'\
    b'\x00\xea\x6e\x00\xec\xe3\x00\xf0\x11\x00\xf2\x3c\x00\xf4\xfb\x00'\
    b'\xf6\x92\x00\xf8\x98\x00\xfc\x10\x00\xfd\xa7\x00\xff\x3e\x01\x00'\
    b'\xd5\x01\x02\x6c\x01\x04\x97\x01\x07\xea\x01\x0a\xf3\x01\x0d\x68'\
    b'\x01\x10\x27\x01\x13\x7a\x01\x15\x5b\x01\x17\x17\x01\x1a\x45\x01'\
    b'\x1d\x73\x01\x1f\x54\x01\x22\x5d\x01\x25\x1c\x01\x28\x25\x01\x2b'\
    b'\x53\x01\x2e\x81\x01\x30\x62\x01\x31\xf9\x01\x35\x02\x01\x38\x30'\
    b'\x01\x3b\x39\x01\x3e\x42\x01\x41\x4b\x01\x44\x2f\x01\x47\x38\x01'\
    b'\x49\xf7\x01\x4d\x94'

_BITMAPS =\
    b'\x00\x00\x00\x00\x00\x00\x00\x00\x00\x00\x00\x00\x00\x00\x00\x00'\
    b'\x00\x00\x00\x00\x00\x00\x00\x00\x00\x00\x00\x00\x1f\xc0\x0f\xfe'\
    b'\x01\xff\xf0\x1e\x0f\x83\xc0\x38\x38\x03\x80\x00\x38\x00\x0f\x80'\
    b'\x7f\xf8\x1f\xff\x83\xff\x38\x7c\x03\x87\x00\x38\x70\x07\x87\x00'\
    b'\x78\x78\x1f\x83\xff\xf8\x1f\xf1\x80\xfc\x1c\x00\x00\x00\x00\x00'\
    b'\x00\x00\x00\x00\x00\x00\x00\x00\x00\x00\x00\x00\x00\x00\x00\x00'\
    b'\x00\x00\x00\x00\x00\x00\x03\x80\x00\x38\x00\x03\x80\x00\x38\x00'\
    b'\x03\x80\x00\x38\x00\x03\x80\x00\x38\xfc\x03\xbf\xf0\x3f\xff\x83'\
    b'\xf0\x78\x3e\x03\xc3\xc0\x1c\x38\x01\xe3\x80\x0e\x38\x00\xe3\x80'\
    b'\x0e\x38\x00\xe3\x80\x0e\x38\x01\xe3\xc0\x1c\x3c\x03\xc3\xf0\x78'\
    b'\x3f\xff\x03\xbf\xe0\x38\xf8\x00\x00\x00\x00\x00\x00\x00\x00\x00'\
    b'\x00\x00\x00\x00\x00\x00\x00\x00\x00\x00\x00\x00\x00\x00\x00\x00'\
    b'\x00\x00\x00\x00\x00\x00\x00\x00\x00\x00\x00\x00\x00\x00\x00\x00'\
    b'\x00\x00\x0f\xc0\x0f\xfc\x07\xff\x83\xe1\xe0\xe0\x3c\x78\x07\x1c'\
    b'\x00\x07\x00\x01\xc0\x00\x70\x00\x1c\x00\x07\x00\x01\xc0\x1c\x38'\
    b'\x07\x0e\x03\x83\xe1\xe0\x7f\xf0\x0f\xf8\x00\xfc\x00\x00\x00\x00'\
    b'\x00\x00\x00\x00\x00\x00\x00\x00\x00\x00\x00\x00\x00\x00\x00\x00'\
    b'\x00\x00\x00\x00\x00\x00\x00\x00\xe0\x00\x0e\x00\x00\xe0\x00\x0e'\
    b'\x00\x00\xe0\x00\x0e\x00\x00\xe0\x0f\x8e\x03\xfe\xe0\x7f\xfe\x0f'\
    b'\x87\xe0\xf0\x1e\x0e\x01\xe1\xc0\x0e\x1c\x00\xe1\xc0\x0e\x1c\x00'\
    b'\xe1\xc0\x0e\x1c\x00\xe1\xc0\x0e\x0e\x01\xe0\xf0\x1e\x07\x87\xe0'\
    b'\x7f\xfe\x03\xfe\xe0\x0f\x8e\x00\x00\x00\x00\x00\x00\x00\x00\x00'\
    b'\x00\x00\x00\x00\x00\x00\x00\x00\x00\x00\x00\x00\x00\x00\x00\x00'\
    b'\x00\x00\x00\x00\x00\x00\x00\x00\x00\x00\x00\x00\x00\x00\x00\x00'\
    b'\x00\x00\x00\x00\x00\x7e\x00\x1f\xf8\x03\xff\xc0\x78\x1e\x0f\x00'\
    b'\xf0\xe0\x07\x1c\x00\x39\xc0\x03\x9f\xff\xf9\xff\xff\x9f\xff\xf9'\
    b'\xc0\x00\x1c\x00\x00\xe0\x03\x8f\x00\x78\x78\x1f\x07\xff\xe0\x1f'\
    b'\xfc\x00\x7f\x00\x00\x00\x00\x00\x00\x00\x00\x00\x00\x00\x00\x00'\
    b'\x00\x00\x00\x00\x00\x00\x00\x00\x00\x00\x01\xf0\xfc\x7f\x1e\x07'\
    b'\x01\xc0\x70\xff\xff\xff\xfc\x70\x1c\x07\x01\xc0\x70\x1c\x07\x01'\
    b'\xc0\x70\x1c\x07\x01\xc0\x70\x1c\x07\x01\xc0\x00\x00\x00\x00\x00'\
    b'\x00\x00\x00\x00\x00\x00\x00\x00\x00\x00\x00\x00\x00\x00\x00\x00'\
    b'\x00\x00\x00\x00\x00\x00\x00\x00\x00\x00\x00\x00\x00\x00\x00\x03'\
    b'\xf1\xc0\xff\xdc\x1f\xff\xc1\xe0\xfc\x3c\x07\xc3\x80\x3c\x78\x03'\
    b'\xc7\x00\x1c\x70\x01\xc7\x00\x1c\x70\x01\xc7\x00\x1c\x70\x01\xc3'\
    b'\x80\x3c\x3c\x07\xc1\xe0\xfc\x1f\xff\xc0\x7f\xdc\x03\xf9\xc0\x00'\
    b'\x1c\x38\x01\xc3\x80\x38\x3e\x07\x81\xff\xf0\x0f\xfe\x00\x3f\x80'\
    b'\x00\x00\x00\x00\x00\x00\x00\x00\x00\x00\x38\x00\x03\x80\x00\x38'\
    b'\x00\x03\x80\x00\x38\x00\x03\x80\x00\x38\x00\x03\x8f\xc0\x3b\xff'\
    b'\x03\xff\xf8\x3f\x07\x83\xc0\x3c\x3c\x01\xc3\x80\x1c\x38\x01\xc3'\
    b'\x80\x1c\x38\x01\xc3\x80\x1c\x38\x01\xc3\x80\x1c\x38\x01\xc3\x80'\
    b'\x1c\x38\x01\xc3\x80\x1c\x38\x01\xc3\x80\x1c\x00\x00\x00\x00\x00'\
    b'\x00\x00\x00\x00\x00\x00\x00\x00\x00\x00\x00\x00\x00\x00\x00\x00'\
    b'\x03\x83\x83\x83\x80\x00\x00\x03\x83\x83\x83\x83\x83\x83\x83\x83'\
    b'\x83\x83\x83\x83\x83\x83\x83\x83\x83\x83\x80\x00\x00\x00\x00\x00'\
    b'\x00\x00\x00\x00\x00\x00\x00\xe0\x38\x0e\x03\x80\x00\x00\x00\x03'\
    b'\x80\xe0\x38\x0e\x03\x80\xe0\x38\x0e\x03\x80\xe0\x38\x0e\x03\x80'\
    b'\xe0\x38\x0e\x03\x80\xe0\x38\x0e\x03\x80\xe0\x78\xfe\x3f\x0f\x80'\
    b'\x00\x00\x00\x00\x00\x00\x00\x00\x00\xe0\x00\x38\x00\x0e\x00\x03'\
    b'\x80\x00\xe0\x00\x38\x00\x0e\x00\x03\x80\xf8\xe0\x7c\x38\x3e\x0e'\
    b'\x1f\x03\x8f\x80\xe7\xc0\x3b\xe0\x0f\xf0\x03\xfe\x00\xfb\xc0\x3c'\
    b'\xf0\x0e\x1e\x03\x83\xc0\xe0\xf0\x38\x1e\x0e\x03\xc3\x80\xf0\xe0'\
    b'\x1e\x38\x03\xc0\x00\x00\x00\x00\x00\x00\x00\x00\x00\x00\x00\x00'\
    b'\x00\x00\x00\x00\x00\x00\x00\x38\x38\x38\x38\x38\x38\x38\x38\x38'\
    b'\x38\x38\x38\x38\x38\x38\x38\x38\x38\x38\x38\x38\x38\x38\x38\x38'\
    b'\x38\x00\x00\x00\x00\x00\x00\x00\x00\x00\x00\x00\x00\x00\x00\x00'\
    b'\x00\x00\x00\x00\x00\x00\x00\x00\x00\x00\x00\x00\x00\x00\x00\x00'\
    b'\x00\x00\x00\x00\x00\x00\x00\x00\x00\x00\x00\x00\x00\x00\x00\x00'\
    b'\x00\x0e\x3e\x07\xe0\x3b\xfe\x7f\xc0\xff\xfb\xff\x83\xe0\xfe\x1f'\
    b'\x0f\x03\xe0\x3c\x3c\x07\x80\x70\xe0\x1c\x01\xc3\x80\x70\x07\x0e'\
    b'\x01\xc0\x1c\x38\x07\x00\x70\xe0\x1c\x01\xc3\x80\x70\x07\x0e\x01'\
    b'\xc0\x1c\x38\x07\x00\x70\xe0\x1c\x01\xc3\x80\x70\x07\x0e\x01\xc0'\
    b'\x1c\x38\x07\x00\x70\xe0\x1c\x01\xc0\x00\x00\x00\x00\x00\x00\x00'\
    b'\x00\x00\x00\x00\x00\x00\x00\x00\x00\x00\x00\x00\x00\x00\x00\x00'\
    b'\x00\x00\x00\x00\x00\x00\x00\x00\x00\x00\x00\x00\x00\x00\x00\x00'\
    b'\x00\x00\x00\x00\x00\x00\x00\x00\x00\x00\x00\x00\x00\x00\x0e\x3f'\
    b'\x00\xe7\xfc\x0e\xff\xe0\xfc\x1e\x0f\x00\xf0\xf0\x07\x0e\x00\x70'\
    b'\xe0\x07\x0e\x00\x70\xe0\x07\x0e\x00\x70\xe0\x07\x0e\x00\x70\xe0'\
    b'\x07\x0e\x00\x70\xe0\x07\x0e\x00\x70\xe0\x07\x0e\x00\x70\x00\x00'\
    b'\x00\x00\x00\x00\x00\x00\x00\x00\x00\x00\x00\x00\x00\x00\x00\x00'\
    b'\x00\x00\x00\x00\x00\x00\x00\x00\x00\x00\x00\x00\x00\x00\x00\x00'\
    b'\x00\x00\x00\x00\x00\x00\x00\x00\x00\x00\x00\x0f\xe0\x03\xff\x80'\
    b'\x7f\xfc\x0f\x81\xe0\xf0\x0f\x0e\x00\x71\xe0\x07\x9c\x00\x39\xc0'\
    b'\x03\x9c\x00\x39\xc0\x03\x9c\x00\x39\xe0\x07\x8e\x00\x70\xf0\x0f'\
    b'\x07\x81\xe0\x3f\xfe\x01\xff\xc0\x07\xf0\x00\x00\x00\x00\x00\x00'\
    b'\x00\x00\x00\x00\x00\x00\x00\x00\x00\x00\x00\x00\x00\x00\x00\x00'\
    b'\x00\x00\x00\x00\x00\x00\x00\x00\x00\x00\x00\x00\x00\x00\x00\x00'\
    b'\x00\x00\x00\x00\x00\x00\x00\x0e\x3f\x00\xef\xfc\x0f\xff\xe0\xfc'\
    b'\x1e\x0f\x80\xf0\xf0\x07\x0e\x00\x78\xe0\x03\x8e\x00\x38\xe0\x03'\
    b'\x8e\x00\x38\xe0\x03\x8e\x00\x78\xf0\x07\x0f\x00\xf0\xfc\x1e\x0f'\
    b'\xff\xe0\xef\xf8\x0e\x7e\x00\xe0\x00\x0e\x00\x00\xe0\x00\x0e\x00'\
    b'\x00\xe0\x00\x0e\x00\x00\xe0\x00\x00\x00\x00\x00\x00\x00\x00\x00'\
    b'\x00\x00\x00\x00\x00\x00\x00\x00\x00\x00\x00\x00\x00\x00\x00\x00'\
    b'\x00\x00\x00\x00\x0f\x8e\x03\xfe\xe0\x7f\xfe\x0f\x87\xe0\xf0\x1e'\
    b'\x0e\x01\xe1\xc0\x0e\x1c\x00\xe1\xc0\x0e\x1c\x00\xe1\xc0\x0e\x1c'\
    b'\x00\xe1\xc0\x0e\x0e\x01\xe0\xf0\x1e\x07\x87\xe0\x7f\xfe\x03\xff'\
    b'\xe0\x0f\xce\x00\x00\xe0\x00\x0e\x00\x00\xe0\x00\x0e\x00\x00\xe0'\
    b'\x00\x0e\x00\x00\xe0\x00\x00\x00\x00\x00\x00\x00\x00\x00\x00\x00'\
    b'\x00\x00\x00\x00\x00\x0e\x78\xef\xcf\xf8\xf8\x0f\x00\xf0\x0e\x00'\
    b'\xe0\x0e\x00\xe0\x0e\x00\xe0\x0e\x00\xe0\x0e\x00\xe0\x0e\x00\xe0'\
    b'\x0e\x00\x00\x00\x00\x00\x00\x00\x00\x00\x00\x00\x00\x00\x00\x00'\
    b'\x00\x00\x00\x00\x00\x00\x00\x00\x00\x00\x00\x00\x00\x00\x00\x00'\
    b'\x00\x00\x00\x00\x00\x03\xf0\x03\xff\x01\xff\xe0\xf0\x3c\x38\x07'\
    b'\x0e\x00\x03\x80\x00\x7c\x00\x1f\xe0\x01\xff\x00\x0f\xf0\x00\x3e'\
    b'\x00\x03\x9c\x00\xe7\x80\x38\xf0\x3e\x3f\xff\x07\xff\x80\x3f\x80'\
    b'\x00\x00\x00\x00\x00\x00\x00\x00\x00\x00\x00\x00\x00\x00\x00\x00'\
    b'\x00\x00\x00\x00\x00\x40\x30\x1c\x07\x01\xc0\x70\x1c\x1f\xe7\xf9'\
    b'\xfe\x1c\x07\x01\xc0\x70\x1c\x07\x01\xc0\x70\x1c\x07\x01\xc0\x70'\
    b'\x1c\x07\xf0\xfc\x1f\x00\x00\x00\x00\x00\x00\x00\x00\x00\x00\x00'\
    b'\x00\x00\x00\x00\x00\x00\x00\x00\x00\x00\x00\x00\x00\x00\x00\x00'\
    b'\x00\x00\x00\x00\x00\x00\x00\x00\x00\x0e\x00\xe0\xe0\x0e\x0e\x00'\
    b'\xe0\xe0\x0e\x0e\x00\xe0\xe0\x0e\x0e\x00\xe0\xe0\x0e\x0e\x00\xe0'\
    b'\xe0\x0e\x0e\x00\xe0\xe0\x0e\x0e\x00\xe0\xe0\x1e\x0f\x01\xe0\xf8'\
    b'\x7e\x07\xff\xe0\x3f\xee\x01\xf8\xe0\x00\x00\x00\x00\x00\x00\x00'\
    b'\x00\x00\x00\x00\x00\x00\x00\x00\x00\x00\x00\x00\x00\x00\x00\x00'\
    b'\x00\x00\x00\x00\x00\x00\x00\x00\x00\x00\x00\x00\x00\x00\x00\x00'\
    b'\x00\x00\x00\x70\x01\xce\x00\xe3\x80\x38\xe0\x0e\x1c\x07\x07\x01'\
    b'\xc1\xc0\x70\x38\x38\x0e\x0e\x01\xc7\x80\x71\xc0\x1c\x70\x03\xb8'\
    b'\x00\xee\x00\x3b\x80\x07\xc0\x01\xf0\x00\x3c\x00\x0e\x00\x00\x00'\
    b'\x00\x00\x00\x00\x00\x00\x00\x00\x00\x00\x00\x00\x00\x00\x00\x00'\
    b'\x00\x00\x00\x00\x00\x00\x00\x00\x00\x00\x00\x00\x00\x00\x00\x00'\
    b'\x00\x00\x00\x00\x00\x00\x00\x00\x00\x00\x00\x00\x00\x00\x00\x00'\
    b'\x00\x38\x03\x80\x7e\x00\xe0\x1d\xc0\x7c\x0e\x70\x1f\x03\x9c\x06'\
    b'\xc0\xe3\x83\xb0\x70\xe0\xee\x1c\x38\x33\x87\x07\x1c\xe3\x81\xc7'\
    b'\x18\xe0\x71\xc7\x38\x0c\xe1\xdc\x03\xb8\x77\x00\xee\x0d\xc0\x1b'\
    b'\x03\xe0\x07\xc0\xf8\x01\xf0\x3e\x00\x38\x07\x00\x0e\x01\xc0\x00'\
    b'\x00\x00\x00\x00\x00\x00\x00\x00\x00\x00\x00\x00\x00\x00\x00\x00'\
    b'\x00\x00\x00\x00\x00\x00\x00\x00\x00\x00\x00\x00\x00\x00\x00\x00'\
    b'\x00\x00\x00\x00\x00\x00\x00\x00\x00\x00\x00\x00\x00\x00\x07\x80'\
    b'\x78\xf0\x3c\x1c\x0e\x07\x87\x80\xf3\xc0\x1c\xe0\x07\xf0\x00\xfc'\
    b'\x00\x1e\x00\x07\x80\x03\xf0\x01\xfc\x00\x73\x80\x3c\xf0\x1e\x1c'\
    b'\x07\x07\x83\xc0\xe1\xe0\x1c\xf0\x07\x80\x00\x00\x00\x00\x00\x00'\
    b'\x00\x00\x00\x00\x00\x00\x00\x00\x00\x00\x00\x00\x00\x00\x00\x00'\
    b'\x00\x00\x00\x00\x00\x00\x00\x00\x00\x00\x00\x00\x00\x00\x00\x00'\
    b'\x00\x01\xc0\x07\x38\x03\x8e\x00\xe3\x80\x38\x70\x1c\x1c\x07\x07'\
    b'\x01\xc0\xe0\xe0\x38\x38\x07\x1c\x01\xc7\x00\x71\xc0\x0e\xe0\x03'\
    b'\xb8\x00\xee\x00\x1f\x00\x07\xc0\x00\xe0\x00\x38\x00\x0e\x00\x07'\
    b'\x00\x01\xc0\x00\xe0\x03\xf8\x00\xfc\x00\x3e\x00\x00\x00\x00\x00'\
    b'\x00\x00\x00\x00\x00\x00\x00\x00\x00\x00\x00\x00\x00\x00\x00\x00'\
    b'\x00\x00\x00\x00\x00\x7f\xff\x9f\xff\xe7\xff\xf8\x00\x3e\x00\x1f'\
    b'\x00\x07\x80\x03\xc0\x01\xe0\x00\xf0\x00\x78\x00\x3c\x00\x1e\x00'\
    b'\x0f\x00\x07\x80\x03\xe0\x01\xf0\x00\x7f\xff\xdf\xff\xf7\xff\xfc'\
    b'\x00\x00\x00\x00\x00\x00\x00\x00\x00\x00\x00\x00\x00\x00\x00\x00'\
    b'\x00\x00\x00\x00\x00\x00\x00\x00\x00\x00\x00\x00\x03\xc0\x00\x07'\
    b'\xc0\x00\x07\xe0\x00\x07\xe0\x00\x0e\xe0\x00\x0e\xf0\x00\x1e\x70'\
    b'\x00\x1c\x78\x00\x1c\x38\x00\x3c\x38\x00\x38\x3c\x00\x78\x1c\x00'\
    b'\x70\x1e\x00\x70\x0e\x00\xf0\x0e\x00\xff\xff\x00\xff\xff\x01\xff'\
    b'\xff\x81\xc0\x07\x83\xc0\x03\x83\xc0\x03\xc3\x80\x03\xc7\x80\x01'\
    b'\xe7\x80\x01\xe7\x00\x00\xef\x00\x00\xf0\x00\x00\x00\x00\x00\x00'\
    b'\x00\x00\x00\x00\x00\x00\x00\x00\x00\x00\x00\x00\x00\x00\x00\x00'\
    b'\x00\x00\x00\x00\x00\x00\x00\x00\x00\x00\x01\xff\xf0\x01\xff\xfc'\
    b'\x01\xff\xfe\x01\xc0\x0f\x01\xc0\x07\x81\xc0\x03\x81\xc0\x03\x81'\
    b'\xc0\x03\x81\xc0\x03\x81\xc0\x07\x01\xc0\x0f\x01\xff\xfe\x01\xff'\
    b'\xfc\x01\xff\xff\x01\xc0\x0f\x81\xc0\x03\x81\xc0\x01\xc1\xc0\x01'\
    b'\xc1\xc0\x01\xc1\xc0\x01\xc1\xc0\x01\xc1\xc0\x03\x81\xc0\x0f\x81'\
    b'\xff\xff\x01\xff\xfe\x01\xff\xf8\x00\x00\x00\x00\x00\x00\x00\x00'\
    b'\x00\x00\x00\x00\x00\x00\x00\x00\x00\x00\x00\x00\x00\x00\x00\x00'\
    b'\x00\x00\x00\x00\x00\x00\x00\x00\x00\x00\x00\x01\xfc\x00\x03\xff'\
    b'\xe0\x01\xff\xfc\x01\xf8\x1f\x80\xf0\x01\xf0\x38\x00\x3c\x1e\x00'\
    b'\x07\x87\x00\x01\xc3\xc0\x00\x00\xe0\x00\x00\x38\x00\x00\x0e\x00'\
    b'\x00\x03\x80\x00\x00\xe0\x00\x00\x38\x00\x00\x0e\x00\x00\x03\x80'\
    b'\x00\x00\x70\x00\x1c\x1c\x00\x07\x87\x80\x03\xc0\xe0\x00\xf0\x3e'\
    b'\x00\x78\x07\xe0\x7e\x00\xff\xff\x00\x0f\xff\x00\x00\xff\x00\x00'\
    b'\x00\x00\x00\x00\x00\x00\x00\x00\x00\x00\x00\x00\x00\x00\x00\x00'\
    b'\x00\x00\x00\x00\x00\x00\x00\x00\x00\x00\x00\x00\x00\x00\x00\x00'\
    b'\x00\x00\x00\x7f\xfc\x00\x1f\xff\xe0\x07\xff\xfc\x01\xc0\x0f\x80'\
    b'\x70\x00\xf0\x1c\x00\x1c\x07\x00\x03\x81\xc0\x00\xe0\x70\x00\x3c'\
    b'\x1c\x00\x07\x07\x00\x01\xc1\xc0\x00\x70\x70\x00\x1c\x1c\x00\x07'\
    b'\x07\x00\x01\xc1\xc0\x00\x70\x70\x00\x1c\x1c\x00\x0e\x07\x00\x03'\
    b'\x81\xc0\x00\xe0\x70\x00\x70\x1c\x00\x3c\x07\x00\x3e\x01\xff\xff'\
    b'\x00\x7f\xff\x80\x1f\xff\x00\x00\x00\x00\x00\x00\x00\x00\x00\x00'\
    b'\x00\x00\x00\x00\x00\x00\x00\x00\x00\x00\x00\x00\x00\x00\x00\x00'\
    b'\x00\x00\x00\x00\x00\x00\x00\x00\x00\x00\x1f\xff\xf8\x1f\xff\xf8'\
    b'\x1f\xff\xf8\x1c\x00\x00\x1c\x00\x00\x1c\x00\x00\x1c\x00\x00\x1c'\
    b'\x00\x00\x1c\x00\x00\x1c\x00\x00\x1c\x00\x00\x1f\xff\xf0\x1f\xff'\
    b'\xf0\x1f\xff\xf0\x1c\x00\x00\x1c\x00\x00\x1c\x00\x00\x1c\x00\x00'\
    b'\x1c\x00\x00\x1c\x00\x00\x1c\x00\x00\x1c\x00\x00\x1c\x00\x00\x1f'\
    b'\xff\xfc\x1f\xff\xfc\x1f\xff\xfc\x00\x00\x00\x00\x00\x00\x00\x00'\
    b'\x00\x00\x00\x00\x00\x00\x00\x00\x00\x00\x00\x00\x00\x00\x00\x00'\
    b'\x00\x00\x00\x00\x00\x00\x00\x00\x1f\xff\xf0\x7f\xff\xc1\xff\xff'\
    b'\x07\x00\x00\x1c\x00\x00\x70\x00\x01\xc0\x00\x07\x00\x00\x1c\x00'\
    b'\x00\x70\x00\x01\xc0\x00\x07\xff\xf0\x1f\xff\xc0\x7f\xff\x01\xc0'\
    b'\x00\x07\x00\x00\x1c\x00\x00\x70\x00\x01\xc0\x00\x07\x00\x00\x1c'\
    b'\x00\x00\x70\x00\x01\xc0\x00\x07\x00\x00\x1c\x00\x00\x70\x00\x00'\
    b'\x00\x00\x00\x00\x00\x00\x00\x00\x00\x00\x00\x00\x00\x00\x00\x00'\
    b'\x00\x00\x00\x00\x00\x00\x00\x00\x00\x00\x00\x00\x00\x00\x00\x00'\
    b'\x00\x00\x7f\x80\x00\x3f\xff\x00\x07\xff\xf8\x00\xf8\x0f\xc0\x1e'\
    b'\x00\x3e\x03\xc0\x00\xe0\x78\x00\x0f\x07\x00\x00\x60\x70\x00\x00'\
    b'\x0e\x00\x00\x00\xe0\x00\x00\x0e\x00\x00\x00\xe0\x00\x00\x0e\x00'\
    b'\x7f\xf0\xe0\x07\xff\x0e\x00\x7f\xf0\xe0\x00\x07\x07\x00\x00\x70'\
    b'\x70\x00\x07\x07\x80\x00\x70\x3c\x00\x07\x01\xe0\x01\xf0\x0f\xc0'\
    b'\x7e\x00\x7f\xff\xc0\x03\xff\xf0\x00\x07\xf8\x00\x00\x00\x00\x00'\
    b'\x00\x00\x00\x00\x00\x00\x00\x00\x00\x00\x00\x00\x00\x00\x00\x00'\
    b'\x00\x00\x00\x00\x00\x00\x00\x00\x00\x00\x00\x00\x00\x00\x00\x00'\
    b'\x00\x07\x00\x03\x81\xc0\x00\xe0\x70\x00\x38\x1c\x00\x0e\x07\x00'\
    b'\x03\x81\xc0\x00\xe0\x70\x00\x38\x1c\x00\x0e\x07\x00\x03\x81\xc0'\
    b'\x00\xe0\x70\x00\x38\x1f\xff\xfe\x07\xff\xff\x81\xff\xff\xe0\x70'\
    b'\x00\x38\x1c\x00\x0e\x07\x00\x03\x81\xc0\x00\xe0\x70\x00\x38\x1c'\
    b'\x00\x0e\x07\x00\x03\x81\xc0\x00\xe0\x70\x00\x38\x1c\x00\x0e\x07'\
    b'\x00\x03\x81\xc0\x00\xe0\x00\x00\x00\x00\x00\x00\x00\x00\x00\x00'\
    b'\x00\x00\x00\x00\x00\x00\x00\x00\x00\x00\x00\x00\x00\x00\x00\x00'\
    b'\x00\x01\xc0\x70\x1c\x07\x01\xc0\x70\x1c\x07\x01\xc0\x70\x1c\x07'\
    b'\x01\xc0\x70\x1c\x07\x01\xc0\x70\x1c\x07\x01\xc0\x70\x1c\x07\x01'\
    b'\xc0\x70\x00\x00\x00\x00\x00\x00\x00\x00\x00\x00\x00\x00\x00\x00'\
    b'\x00\x00\x00\x00\x00\x38\x00\x0e\x00\x03\x80\x00\xe0\x00\x38\x00'\
    b'\x0e\x00\x03\x80\x00\xe0\x00\x38\x00\x0e\x00\x03\x80\x00\xe0\x00'\
    b'\x38\x00\x0e\x00\x03\x80\x00\xe0\x00\x38\x00\x0e\x1c\x03\x87\x00'\
    b'\xe1\xe0\x38\x78\x1c\x0f\x0f\x03\xff\xc0\x7f\xe0\x07\xe0\x00\x00'\
    b'\x00\x00\x00\x00\x00\x00\x00\x00\x00\x00\x00\x00\x00\x00\x00\x00'\
    b'\x00\x00\x00\x00\x00\x00\x00\x00\x00\x00\x1c\x00\x3e\x1c\x00\x7c'\
    b'\x1c\x00\xf8\x1c\x01\xf0\x1c\x03\xe0\x1c\x07\xc0\x1c\x0f\x80\x1c'\
    b'\x1f\x00\x1c\x3e\x00\x1c\x7c\x00\x1c\xf8\x00\x1d\xf8\x00\x1f\xfc'\
    b'\x00\x1f\xde\x00\x1f\x9f\x00\x1f\x0f\x00\x1e\x07\x80\x1c\x07\xc0'\
    b'\x1c\x03\xe0\x1c\x01\xe0\x1c\x00\xf0\x1c\x00\xf8\x1c\x00\x78\x1c'\
    b'\x00\x3c\x1c\x00\x3e\x1c\x00\x1f\x00\x00\x00\x00\x00\x00\x00\x00'\
    b'\x00\x00\x00\x00\x00\x00\x00\x00\x00\x00\x00\x00\x00\x00\x00\x00'\
    b'\x00\x00\x00\x00\x00\x00\x00\x1c\x00\x01\xc0\x00\x1c\x00\x01\xc0'\
    b'\x00\x1c\x00\x01\xc0\x00\x1c\x00\x01\xc0\x00\x1c\x00\x01\xc0\x00'\
    b'\x1c\x00\x01\xc0\x00\x1c\x00\x01\xc0\x00\x1c\x00\x01\xc0\x00\x1c'\
    b'\x00\x01\xc0\x00\x1c\x00\x01\xc0\x00\x1c\x00\x01\xc0\x00\x1c\x00'\
    b'\x01\xff\xfe\x1f\xff\xe1\xff\xfe\x00\x00\x00\x00\x00\x00\x00\x00'\
    b'\x00\x00\x00\x00\x00\x00\x00\x00\x00\x00\x00\x00\x00\x00\x00\x00'\
    b'\x00\x00\x00\x00\x00\x00\x00\x00\x03\xe0\x00\x1f\x0f\xc0\x00\xfc'\
    b'\x3f\x00\x03\xf0\xfc\x00\x0f\xc3\xf8\x00\x7f\x0e\xe0\x01\xfc\x3b'\
    b'\x80\x07\x70\xef\x00\x3d\xc3\x9c\x00\xe7\x0e\x78\x03\x9c\x39\xe0'\
    b'\x1e\x70\xe3\x80\x71\xc3\x8f\x01\xc7\x0e\x1c\x0f\x1c\x38\x70\x38'\
    b'\x70\xe1\xe1\xe1\xc3\x83\x87\x07\x0e\x0f\x1c\x1c\x38\x3c\xf0\x70'\
    b'\xe0\x73\x81\xc3\x81\xee\x07\x0e\x03\xf0\x1c\x38\x0f\xc0\x70\xe0'\
    b'\x3f\x01\xc3\x80\x78\x07\x0e\x01\xe0\x1c\x00\x00\x00\x00\x00\x00'\
    b'\x00\x00\x00\x00\x00\x00\x00\x00\x00\x00\x00\x00\x00\x00\x00\x00'\
    b'\x00\x00\x00\x00\x00\x00\x00\x00\x00\x00\x00\x00\x00\x00\x00\x00'\
    b'\x00\x07\x00\x03\x81\xe0\x00\xe0\x7c\x00\x38\x1f\x00\x0e\x07\xe0'\
    b'\x03\x81\xfc\x00\xe0\x77\x00\x38\x1c\xe0\x0e\x07\x3c\x03\x81\xc7'\
    b'\x00\xe0\x70\xe0\x38\x1c\x3c\x0e\x07\x07\x03\x81\xc0\xe0\xe0\x70'\
    b'\x3c\x38\x1c\x07\x0e\x07\x00\xe3\x81\xc0\x3c\xe0\x70\x07\x38\x1c'\
    b'\x00\xee\x07\x00\x3f\x81\xc0\x07\xe0\x70\x00\xf8\x1c\x00\x3e\x07'\
    b'\x00\x07\x81\xc0\x00\xe0\x00\x00\x00\x00\x00\x00\x00\x00\x00\x00'\
    b'\x00\x00\x00\x00\x00\x00\x00\x00\x00\x00\x00\x00\x00\x00\x00\x00'\
    b'\x00\x00\x00\x00\x00\x00\x00\x00\x00\x00\x00\x03\xfc\x00\x01\xff'\
    b'\xf8\x00\x3f\xff\xc0\x07\xe0\x7e\x00\xf8\x01\xf0\x0f\x00\x0f\x01'\
    b'\xe0\x00\x78\x1c\x00\x03\x81\xc0\x00\x38\x38\x00\x01\xc3\x80\x00'\
    b'\x1c\x38\x00\x01\xc3\x80\x00\x1c\x38\x00\x01\xc3\x80\x00\x1c\x38'\
    b'\x00\x01\xc3\x80\x00\x1c\x1c\x00\x03\x81\xc0\x00\x38\x1e\x00\x07'\
    b'\x80\xf0\x00\xf0\x0f\x80\x1f\x00\x7e\x07\xe0\x03\xff\xfc\x00\x1f'\
    b'\xff\x80\x00\x3f\xc0\x00\x00\x00\x00\x00\x00\x00\x00\x00\x00\x00'\
    b'\x00\x00\x00\x00\x00\x00\x00\x00\x00\x00\x00\x00\x00\x00\x00\x00'\
    b'\x00\x00\x00\x00\x00\x00\x00\x00\x00\x00\x1f\xff\x80\x1f\xff\xe0'\
    b'\x1f\xff\xf0\x1c\x00\x78\x1c\x00\x38\x1c\x00\x3c\x1c\x00\x1c\x1c'\
    b'\x00\x1c\x1c\x00\x1c\x1c\x00\x1c\x1c\x00\x3c\x1c\x00\x38\x1c\x00'\
    b'\xf8\x1f\xff\xf0\x1f\xff\xe0\x1f\xff\x80\x1c\x00\x00\x1c\x00\x00'\
    b'\x1c\x00\x00\x1c\x00\x00\x1c\x00\x00\x1c\x00\x00\x1c\x00\x00\x1c'\
    b'\x00\x00\x1c\x00\x00\x1c\x00\x00\x00\x00\x00\x00\x00\x00\x00\x00'\
    b'\x00\x00\x00\x00\x00\x00\x00\x00\x00\x00\x00\x00\x00\x00\x00\x00'\
    b'\x00\x00\x00\x00\x00\x00\x00\x00\x00\x00\x00\x00\x1f\xc0\x00\x0f'\
    b'\xff\x00\x01\xff\xfc\x00\x3e\x07\xe0\x07\x80\x1e\x00\xf0\x00\xf0'\
    b'\x1e\x00\x07\x81\xc0\x00\x38\x1c\x00\x03\x83\x80\x00\x1c\x38\x00'\
    b'\x01\xc3\x80\x00\x1c\x38\x00\x01\xc3\x80\x00\x1c\x38\x00\x01\xc3'\
    b'\x80\x00\x1c\x38\x00\x01\xc1\xc0\x00\x38\x1c\x00\x03\x81\xe0\x18'\
    b'\x30\x0f\x01\xe7\x00\x78\x0f\xe0\x03\xe0\x3c\x00\x1f\xff\xf0\x00'\
    b'\xff\xe7\x80\x01\xf8\x3c\x00\x00\x00\x80\x00\x00\x00\x00\x00\x00'\
    b'\x00\x00\x00\x00\x00\x00\x00\x00\x00\x00\x00\x00\x00\x00\x00\x00'\
    b'\x00\x00\x00\x00\x00\x00\x00\x00\x00\x00\x00\x01\xff\xfe\x00\x7f'\
    b'\xff\xc0\x1f\xff\xf8\x07\x00\x1f\x01\xc0\x01\xe0\x70\x00\x38\x1c'\
    b'\x00\x0e\x07\x00\x03\x81\xc0\x00\xe0\x70\x00\x78\x1c\x00\x3c\x07'\
    b'\x00\x1f\x01\xff\xff\x80\x7f\xff\xc0\x1f\xff\x80\x07\x01\xe0\x01'\
    b'\xc0\x3e\x00\x70\x07\x80\x1c\x00\xf0\x07\x00\x1e\x01\xc0\x07\x80'\
    b'\x70\x00\xf0\x1c\x00\x1e\x07\x00\x07\x81\xc0\x00\xf0\x70\x00\x1e'\
    b'\x00\x00\x00\x00\x00\x00\x00\x00\x00\x00\x00\x00\x00\x00\x00\x00'\
    b'\x00\x00\x00\x00\x00\x00\x00\x00\x00\x00\x00\x00\x00\x00\x00\x00'\
    b'\x00\x00\x00\x03\xfc\x00\x0f\xff\x00\x1f\xff\x80\x3e\x07\xc0\x78'\
    b'\x01\xe0\x70\x00\xe0\x70\x00\xe0\x70\x00\x00\x70\x00\x00\x3c\x00'\
    b'\x00\x3f\x00\x00\x1f\xf0\x00\x07\xff\x00\x01\xff\x80\x00\x1f\xc0'\
    b'\x00\x01\xe0\x00\x00\xf0\x70\x00\x70\x70\x00\x70\x78\x00\x70\x38'\
    b'\x00\x70\x3c\x00\xe0\x1f\x03\xe0\x0f\xff\xc0\x07\xff\x80\x01\xfe'\
    b'\x00\x00\x00\x00\x00\x00\x00\x00\x00\x00\x00\x00\x00\x00\x00\x00'\
    b'\x00\x00\x00\x00\x00\x00\x00\x00\x00\x00\x00\x00\x00\x00\x00\x00'\
    b'\x00\xff\xff\xe3\xff\xff\x8f\xff\xfe\x00\x38\x00\x00\xe0\x00\x03'\
    b'\x80\x00\x0e\x00\x00\x38\x00\x00\xe0\x00\x03\x80\x00\x0e\x00\x00'\
    b'\x38\x00\x00\xe0\x00\x03\x80\x00\x0e\x00\x00\x38\x00\x00\xe0\x00'\
    b'\x03\x80\x00\x0e\x00\x00\x38\x00\x00\xe0\x00\x03\x80\x00\x0e\x00'\
    b'\x00\x38\x00\x00\xe0\x00\x03\x80\x00\x00\x00\x00\x00\x00\x00\x00'\
    b'\x00\x00\x00\x00\x00\x00\x00\x00\x00\x00\x00\x00\x00\x00\x00\x00'\
    b'\x00\x00\x00\x00\x00\x00\x00\x00\x01\xc0\x00\xe0\x70\x00\x38\x1c'\
    b'\x00\x0e\x07\x00\x03\x81\xc0\x00\xe0\x70\x00\x38\x1c\x00\x0e\x07'\
    b'\x00\x03\x81\xc0\x00\xe0\x70\x00\x38\x1c\x00\x0e\x07\x00\x03\x81'\
    b'\xc0\x00\xe0\x70\x00\x38\x1c\x00\x0e\x07\x00\x03\x81\xc0\x00\xe0'\
    b'\x70\x00\x38\x1c\x00\x0e\x07\x80\x07\x80\xe0\x01\xc0\x3c\x00\xf0'\
    b'\x07\xc0\xf8\x01\xff\xfc\x00\x1f\xfe\x00\x01\xfe\x00\x00\x00\x00'\
    b'\x00\x00\x00\x00\x00\x00\x00\x00\x00\x00\x00\x00\x00\x00\x00\x00'\
    b'\x00\x00\x00\x00\x00\x00\x00\x00\x00\x00\x00\x00\x00\x00\x00\x03'\
    b'\xc0\x00\x3d\xe0\x00\x79\xe0\x00\x79\xe0\x00\x78\xf0\x00\xf0\xf0'\
    b'\x00\xf0\x70\x00\xf0\x78\x01\xe0\x78\x01\xe0\x38\x01\xc0\x3c\x03'\
    b'\xc0\x3c\x03\xc0\x1c\x03\x80\x1e\x07\x80\x0e\x07\x00\x0f\x0f\x00'\
    b'\x0f\x0f\x00\x07\x0e\x00\x07\x9e\x00\x03\x9e\x00\x03\x9c\x00\x03'\
    b'\xfc\x00\x01\xf8\x00\x01\xf8\x00\x01\xf8\x00\x00\xf0\x00\x00\x00'\
    b'\x00\x00\x00\x00\x00\x00\x00\x00\x00\x00\x00\x00\x00\x00\x00\x00'\
    b'\x00\x00\x00\x00\x00\x00\x00\x00\x00\x00\x00\x00\x00\x00\x00\x00'\
    b'\x00\x00\x00\x01\xc0\x03\x80\x0e\x70\x00\xe0\x03\x8e\x00\x7c\x01'\
    b'\xc3\x80\x1b\x00\x70\xe0\x06\xc0\x1c\x38\x03\xb8\x07\x07\x00\xee'\
    b'\x03\x81\xc0\x33\x80\xe0\x70\x1c\x60\x38\x0c\x07\x1c\x0c\x03\x81'\
    b'\x87\x07\x00\xe0\xe1\xc1\xc0\x38\x38\x30\x70\x06\x0e\x0e\x18\x01'\
    b'\xc3\x03\x8e\x00\x71\xc0\xe3\x80\x1c\x70\x18\xe0\x03\x18\x07\x70'\
    b'\x00\xee\x01\xdc\x00\x3b\x80\x77\x00\x06\xe0\x0d\x80\x01\xb0\x03'\
    b'\x60\x00\x7c\x00\xf8\x00\x1f\x00\x3e\x00\x03\x80\x07\x00\x00\xe0'\
    b'\x01\xc0\x00\x00\x00\x00\x00\x00\x00\x00\x00\x00\x00\x00\x00\x00'\
    b'\x00\x00\x00\x00\x00\x00\x00\x00\x00\x00\x00\x00\x00\x00\x00\x00'\
    b'\x00\x00\x00\x00\x00\x00\x00\x00\x00\x00\x00\x00\x78\x00\x0e\x3c'\
    b'\x00\x1c\x1e\x00\x38\x0f\x00\x70\x0f\x00\xf0\x07\x81\xe0\x03\xc1'\
    b'\xc0\x03\xe3\xc0\x01\xe7\x80\x00\xff\x00\x00\x7e\x00\x00\x7e\x00'\
    b'\x00\x3c\x00\x00\x7e\x00\x00\xff\x00\x00\xff\x00\x01\xe7\x80\x03'\
    b'\xc3\xc0\x03\xc3\xe0\x07\x81\xe0\x0f\x00\xf0\x1e\x00\x78\x1e\x00'\
    b'\x78\x3c\x00\x3c\x78\x00\x1e\xf0\x00\x0f\x00\x00\x00\x00\x00\x00'\
    b'\x00\x00\x00\x00\x00\x00\x00\x00\x00\x00\x00\x00\x00\x00\x00\x00'\
    b'\x00\x00\x00\x00\x00\x00\x00\x00\x00\x00\x00\x78\x00\x1e\x3c\x00'\
    b'\x3c\x3c\x00\x78\x1e\x00\x78\x0f\x00\xf0\x0f\x00\xe0\x07\x81\xe0'\
    b'\x07\x83\xc0\x03\xc3\x80\x01\xc7\x80\x01\xe7\x00\x00\xee\x00\x00'\
    b'\xfe\x00\x00\x7c\x00\x00\x38\x00\x00\x38\x00\x00\x38\x00\x00\x38'\
    b'\x00\x00\x38\x00\x00\x38\x00\x00\x38\x00\x00\x38\x00\x00\x38\x00'\
    b'\x00\x38\x00\x00\x38\x00\x00\x38\x00\x00\x00\x00\x00\x00\x00\x00'\
    b'\x00\x00\x00\x00\x00\x00\x00\x00\x00\x00\x00\x00\x00\x00\x00\x00'\
    b'\x00\x00\x00\x00\x00\x00\x00\x00\x00\x3f\xff\xf8\xff\xff\xe3\xff'\
    b'\xff\x80\x00\x1e\x00\x00\xf0\x00\x07\x80\x00\x3c\x00\x01\xe0\x00'\
    b'\x0f\x80\x00\x3c\x00\x01\xe0\x00\x0f\x00\x00\x78\x00\x03\xe0\x00'\
    b'\x0f\x00\x00\x78\x00\x03\xc0\x00\x1e\x00\x00\x78\x00\x03\xc0\x00'\
    b'\x1e\x00\x00\xf0\x00\x07\x80\x00\x1f\xff\xfe\x7f\xff\xf9\xff\xff'\
    b'\xe0\x00\x00\x00\x00\x00\x00\x00\x00\x00\x00\x00\x00\x00\x00\x00'\
    b'\x00\x00\x00\x00\x00\x00\x00\x00\x00\x00\x00\x00\x00\x00\x00\x00'\
    b'\x00\x00\x00\x00\x00\x3e\x00\x1f\xf0\x07\xfe\x00\xf1\xe0\x3c\x1e'\
    b'\x07\x01\xc0\xe0\x38\x38\x03\x87\x00\x70\xe0\x0e\x1c\x01\xc3\x80'\
    b'\x38\x70\x07\x0e\x00\xe1\xc0\x1c\x38\x03\x83\x80\xe0\x70\x1c\x0f'\
    b'\x07\x80\xf1\xe0\x1f\xfc\x01\xff\x00\x0f\x80\x00\x00\x00\x00\x00'\
    b'\x00\x00\x00\x00\x00\x00\x00\x00\x00\x00\x00\x00\x00\x00\x00\x00'\
    b'\x00\x00\x00\x00\x00\x00\x00\x00\x00\x00\x00\x00\x00\x38\x00\x0f'\
    b'\x00\x03\xe0\x00\xfc\x00\x3b\x80\x0e\x70\x00\x8e\x00\x01\xc0\x00'\
    b'\x38\x00\x07\x00\x00\xe0\x00\x1c\x00\x03\x80\x00\x70\x00\x0e\x00'\
    b'\x01\xc0\x00\x38\x00\x07\x00\x00\xe0\x00\x1c\x00\x03\x80\x00\x70'\
    b'\x00\x0e\x00\x00\x00\x00\x00\x00\x00\x00\x00\x00\x00\x00\x00\x00'\
    b'\x00\x00\x00\x00\x00\x00\x00\x00\x00\x00\x00\x00\x00\x00\x00\x00'\
    b'\x00\x00\x00\x00\x00\xf8\x00\x7f\xc0\x1f\xfc\x07\x87\x81\xe0\x78'\
    b'\x38\x07\x02\x00\xe0\x00\x1c\x00\x03\x80\x00\xe0\x00\x3c\x00\x0f'\
    b'\x00\x03\xc0\x00\xe0\x00\x38\x00\x0e\x00\x03\x80\x00\x60\x00\x1c'\
    b'\x00\x03\x00\x00\xff\xf8\x1f\xff\x03\xff\xe0\x00\x00\x00\x00\x00'\
    b'\x00\x00\x00\x00\x00\x00\x00\x00\x00\x00\x00\x00\x00\x00\x00\x00'\
    b'\x00\x00\x00\x00\x00\x00\x00\x00\x00\x00\x00\x00\x3f\xfe\x07\xff'\
    b'\xc0\xff\xf0\x00\x0c\x00\x03\x80\x00\xe0\x00\x38\x00\x0e\x00\x01'\
    b'\xf0\x00\x7f\x80\x1f\xf8\x01\x8f\x00\x00\xf0\x00\x0e\x00\x01\xc0'\
    b'\x00\x38\x00\x07\x04\x01\xe1\xc0\x38\x3e\x1f\x03\xff\xc0\x3f\xf0'\
    b'\x01\xf8\x00\x00\x00\x00\x00\x00\x00\x00\x00\x00\x00\x00\x00\x00'\
    b'\x00\x00\x00\x00\x00\x00\x00\x00\x00\x00\x00\x00\x00\x00\x00\x00'\
    b'\x00\x00\x00\x00\x00\xf8\x00\x3f\x00\x0f\xe0\x03\xdc\x00\x73\x80'\
    b'\x1c\x70\x03\x8e\x00\x61\xc0\x1c\x38\x03\x87\x00\x60\xe0\x1c\x1c'\
    b'\x03\x83\x80\xe0\x70\x3f\xff\xc7\xff\xf8\xff\xff\x00\x07\x00\x00'\
    b'\xe0\x00\x1c\x00\x03\x80\x00\x70\x00\x0e\x00\x00\x00\x00\x00\x00'\
    b'\x00\x00\x00\x00\x00\x00\x00\x00\x00\x00\x00\x00\x00\x00\x00\x00'\
    b'\x00\x00\x00\x00\x00\x00\x00\x00\x00\x00\x00\x00\x1f\xfc\x03\xff'\
    b'\x80\x7f\xf0\x1c\x00\x03\x80\x00\x70\x00\x0e\x00\x01\xdf\x00\x3f'\
    b'\xf8\x0f\xff\x01\xe1\xf0\x30\x0e\x00\x00\xe0\x00\x1c\x00\x03\x80'\
    b'\x00\x70\x00\x0e\x08\x03\xc3\x80\x70\x7c\x3e\x07\xff\x80\x7f\xe0'\
    b'\x03\xf0\x00\x00\x00\x00\x00\x00\x00\x00\x00\x00\x00\x00\x00\x00'\
    b'\x00\x00\x00\x00\x00\x00\x00\x00\x00\x00\x00\x00\x00\x00\x00\x00'\
    b'\x00\x00\x00\x00\x01\xf0\x00\xfe\x00\x7f\xc0\x1f\x80\x07\x80\x01'\
    b'\xe0\x00\x38\x00\x0e\x00\x01\x8f\xc0\x77\xfc\x0f\xff\xc1\xf8\x7c'\
    b'\x3c\x03\x87\x00\x78\xe0\x07\x1c\x00\xe3\x80\x1c\x30\x07\x87\x00'\
    b'\xe0\xf8\x7c\x0f\xff\x00\xff\xc0\x07\xe0\x00\x00\x00\x00\x00\x00'\
    b'\x00\x00\x00\x00\x00\x00\x00\x00\x00\x00\x00\x00\x00\x00\x00\x00'\
    b'\x00\x00\x00\x00\x00\x00\x00\x00\x00\x00\x00\x03\xff\xf0\x7f\xfe'\
    b'\x0f\xff\xc0\x00\x38\x00\x06\x00\x01\xc0\x00\x70\x00\x0e\x00\x03'\
    b'\x80\x00\x70\x00\x1c\x00\x03\x80\x00\xe0\x00\x1c\x00\x07\x00\x00'\
    b'\xe0\x00\x38\x00\x07\x00\x00\xe0\x00\x18\x00\x07\x00\x00\xe0\x00'\
    b'\x1c\x00\x00\x00\x00\x00\x00\x00\x00\x00\x00\x00\x00\x00\x00\x00'\
    b'\x00\x00\x00\x00\x00\x00\x00\x00\x00\x00\x00\x00\x00\x00\x00\x00'\
    b'\x00\x00\x00\x00\x3e\x00\x1f\xf0\x07\xff\x01\xf1\xf0\x3c\x1e\x07'\
    b'\x01\xc0\xe0\x38\x1c\x07\x01\xe3\xc0\x1f\xf0\x01\xfc\x00\xff\xe0'\
    b'\x3c\x1e\x07\x01\xc1\xc0\x1c\x38\x03\x87\x00\x70\xe0\x0e\x1e\x03'\
    b'\xc1\xe0\xf0\x3f\xfe\x01\xff\x00\x1f\xc0\x00\x00\x00\x00\x00\x00'\
    b'\x00\x00\x00\x00\x00\x00\x00\x00\x00\x00\x00\x00\x00\x00\x00\x00'\
    b'\x00\x00\x00\x00\x00\x00\x00\x00\x00\x00\x00\x00\xfc\x00\x3f\xe0'\
    b'\x0f\xfe\x03\xc1\xe0\xf0\x1c\x1c\x01\x83\x80\x38\x70\x07\x0e\x00'\
    b'\xe1\xc0\x1c\x3c\x07\x83\xc1\xf0\x3f\xfe\x03\xfd\xc0\x3f\x30\x00'\
    b'\x0e\x00\x03\xc0\x00\x70\x00\x3c\x00\x1f\x00\x3f\xc0\x07\xf0\x00'\
    b'\xf0\x00\x00\x00\x00\x00\x00\x00\x00\x00\x00\x00\x00\x00\x00\x00'\
    b'\x00\x00\x00\x00\x00\x00\x00\x00\x00\x00\x00\x00\x07\x00\xe0\x1c'\
    b'\x03\x80\x70\x0e\x01\xc0\x38\x07\x00\xe0\x1c\x03\x80\x70\x0e\x01'\
    b'\xc0\x38\x00\x00\x00\x00\x03\x00\x70\x0e\x01\x80\x00\x00\x00\x00'\
    b'\x00\x00\x00\x00\x00\x00\x00\x00\x00\x00\x00\x00\x00\x00\x00\x00'\
    b'\x00\x00\x00\x00\x00\x00\x00\x61\x80\x30\xc0\x18\x60\x1c\x70\x0c'\
    b'\x30\x06\x18\x03\x0c\x3f\xff\xdf\xff\xe0\x61\x80\x30\xc0\x30\xc0'\
    b'\x18\x60\xff\xff\x7f\xff\x86\x18\x03\x0c\x01\x86\x01\xc7\x00\xc3'\
    b'\x00\x61\x80\x30\xc0\x00\x00\x00\x00\x00\x00\x00\x00\x00\x00\x00'\
    b'\x00\x00\x00\x00\x00\x00\x00\x00\x00\x00\x00\x00\x7c\x03\xfe\x0e'\
    b'\x0e\x18\x0c\x60\x0c\xc0\x19\x80\x33\x00\x66\x00\xc6\x03\x0e\x0e'\
    b'\x0f\xf8\x07\xc0\x00\x00\x00\x00\x00\x00\x00\x00\x00\x00\x00\x00'\
    b'\x00\x00\x00\x00\x00\x00\x00\x00\x00\x00\x00\x00\x00\x00\x00\x00'\
    b'\x00\x00\x00\x00\x00\x00\x00\x00\x00\x00\x00\x00\x00\x00\x00\x1c'\
    b'\x00\x0e\x00\x01\xc0\x00\x70\x00\x0e\x00\x01\xc0\x00\x38\x00\x07'\
    b'\x00\x00\xe0\x00\x1c\x00\x03\x80\x00\x70\x00\x0e\x00\x01\xc0\x00'\
    b'\x38\x00\x0e\x00\x07\x00\x00\x38\x00\x07\x80\x00\x70\x00\x0e\x00'\
    b'\x01\xc0\x00\x38\x00\x07\x00\x00\xe0\x00\x1c\x00\x03\x80\x00\x70'\
    b'\x00\x0e\x00\x01\xc0\x00\x38\x00\x03\x80\x00\x70\x00\x03\x80\x00'\
    b'\x00\x00\x00\x00\x00\x00\x00\x00\x00\x00\x00\x00\x00\x00\x00\x00'\
    b'\x00\x00\x00\x00\x00\x00\x00\x00\x00\x00\x00\x00\x00\x00\x00\x00'\
    b'\x00\x00\x00\x00\x00\x00\x00\x00\x00\x00\x00\x00\x00\x00\x00\x00'\
    b'\x00\x00\x00\x00\x00\x00\x00\x00\x00\x07\x00\x00\x78\x00\x07\x00'\
    b'\x00\x70\x00\x0e\x00\x01\xc0\x00\x38\x00\x07\x00\x00\xe0\x00\x1c'\
    b'\x00\x03\x80\x00\x70\x00\x0e\x00\x01\xc0\x00\x38\x00\x07\x80\x00'\
    b'\x70\x00\x03\x80\x01\xc0\x00\x78\x00\x0e\x00\x01\xc0\x00\x38\x00'\
    b'\x07\x00\x00\xe0\x00\x1c\x00\x03\x80\x00\x70\x00\x0e\x00\x01\xc0'\
    b'\x00\x38\x00\x0e\x00\x01\xc0\x00\xe0\x00\x00\x00\x00\x00\x00\x00'\
    b'\x00\x00\x00\x00\x00\x00\x00\x00\x01\x80\x00\x30\x00\x1f\x80\x0f'\
    b'\xfc\x03\xff\xc0\x73\x38\x1e\x63\x83\x8c\x20\x71\x80\x0e\x30\x01'\
    b'\xe6\x00\x1e\xc0\x01\xf8\x00\x1f\xc0\x00\xfe\x00\x0f\xe0\x01\x9e'\
    b'\x00\x31\xe0\x06\x1c\x60\xc3\x8e\x18\x70\xf3\x3e\x0f\xff\x80\xff'\
    b'\xe0\x07\xf0\x00\x30\x00\x06\x00\x00\xc0\x00\x00\x00\x00\x00\x00'\
    b'\x00\x00\x00\x00\x00\x00\x00\x00\x00\x00\x00\x00\x00\x00\x00\x00'\
    b'\x00\x00\x00\x00\x00\x00\x00\x00\x00\x00\x00\x00\x00\x03\xf0\x02'\
    b'\x00\x3f\xc0\x38\x03\xff\x01\x80\x3c\x3c\x18\x01\xc0\xe0\xc0\x0e'\
    b'\x07\x0c\x00\x70\x38\xe0\x03\xc3\xc6\x00\x0f\xfc\x60\x00\x3f\xc7'\
    b'\x00\x00\xfc\x30\x00\x00\x03\x00\x00\x00\x18\x7e\x00\x01\x87\xf8'\
    b'\x00\x1c\x7f\xe0\x00\xc7\x87\x80\x0c\x38\x1c\x00\xe1\xc0\xe0\x06'\
    b'\x0e\x07\x00\x60\x78\x78\x03\x01\xff\x80\x30\x07\xf8\x03\x80\x1f'\
    b'\x80\x08\x00\x00\x00\x00\x00\x00\x00\x00\x00\x00\x00\x00\x00\x00'\
    b'\x00\x00\x00\x00\x00\x00\x00\x00\x00\x00\x00\x00\x00\x00\x00\x00'\
    b'\x00\x00\x00\x00\x00\x00\x00\x00\x00\x00\x00\x00\x00\x00\x00\x00'\
    b'\x00\x01\xf0\x00\x00\xc6\x00\x00\x60\xc0\x00\x38\x30\x00\x0e\x0c'\
    b'\x00\x03\x83\x00\x00\xf1\x80\x00\x1c\x60\x00\x07\xb3\xf8\x00\xf8'\
    b'\x7c\x00\x7c\x0e\x00\x77\x83\x00\x31\xe0\x80\x18\x3c\x60\x0c\x0f'\
    b'\x10\x07\x01\xc8\x01\xc0\x7e\x00\x70\x0f\x00\x1c\x01\xe0\x07\x80'\
    b'\xfe\x18\xf0\xff\xfc\x3f\xf0\xfe\x03\xf0\x1e\x00\x00\x00\x00\x00'\
    b'\x00\x00\x00\x00\x00\x00\x00\x00\x00\x00\x00\x00\x00\x00\x00\x00'\
    b'\x00\x00\x00\x00\x00\x00\x00\x00\x00\x00\x00\x00\x0e\x01\xc0\x30'\
    b'\x0e\x01\x80\x30\x0c\x01\x80\x00\x00\x00\x00\x00\x00\x00\x00\x00'\
    b'\x00\x00\x00\x00\x00\x00\x00\x00\x00\x00\x00\x00\x00\x00\x00\x00'\
    b'\x00\x00\x00\x00\x00\x00\x00\x00\x00\x00\x00\x00\x00\x00\x00\x00'\
    b'\x06\x00\xc0\x18\x01\x80\x30\x03\x00\x60\x06\x00\x60\x0c\x00\xc0'\
    b'\x0c\x00\xc0\x0c\x00\xc0\x0c\x00\xc0\x0c\x00\x60\x06\x00\x60\x03'\
    b'\x00\x30\x01\x80\x18\x00\xc0\x06\x00\x00\x00\x00\x00\x00\x00\x00'\
    b'\x00\x00\x00\x00\x00\x00\x00\x18\x00\xc0\x06\x00\x60\x03\x00\x30'\
    b'\x01\x80\x18\x01\x80\x0c\x00\xc0\x0c\x00\xc0\x0c\x00\xc0\x0c\x00'\
    b'\xc0\x0c\x01\x80\x18\x01\x80\x30\x03\x00\x60\x06\x00\xc0\x18\x00'\
    b'\x00\x00\x00\x00\x00\x38\x00\x03\x80\x00\x38\x00\x43\x84\x0e\x31'\
    b'\xe0\xf3\x3e\x03\xf7\x80\x0f\xe0\x00\x38\x00\x0f\xe0\x03\xb7\x80'\
    b'\xf3\x3e\x0e\x30\xe0\x03\x84\x00\x38\x00\x03\x80\x00\x38\x00\x00'\
    b'\x00\x00\x00\x00\x00\x00\x00\x00\x00\x00\x00\x00\x00\x00\x00\x00'\
    b'\x00\x00\x00\x00\x00\x00\x00\x00\x00\x00\x00\x00\x00\x00\x00\x00'\
    b'\x00\x00\x00\x00\x00\x00\x00\x00\x00\x00\x00\x00\x00\x00\x00\x00'\
    b'\x00\x00\x00\x00\x00\x00\x00\x00\x00\x00\x00\x00\x00\x00\x00\x00'\
    b'\x00\x00\x00\x00\x01\x00\x38\x03\x80\x30\x00\x00\x00\x00\x00\x00'\
    b'\x00\x00\x00\x00\x00\x38\x07\x80\x70\x0f\x00\xe0\x0c\x01\xc0\x18'\
    b'\x00\x00\x00\x00\x00\x00\x00\x00\x00\x00\x00\x00\x00\x00\x00\x00'\
    b'\x00\x00\x00\x00\x00\x00\x00\x00\x00\x00\x00\x00\x00\x00\x00\x00'\
    b'\x00\x00\x00\x00\x00\x00\x00\x00\x00\x00\x00\x08\x00\x00\xe0\x00'\
    b'\x0f\x80\x00\xf8\x00\x0f\x80\x01\xf8\x00\x1f\x80\x01\xf0\x00\x0f'\
    b'\x00\x00\x3c\x00\x00\x7c\x00\x00\x7c\x00\x00\x7e\x00\x00\x7e\x00'\
    b'\x00\x7e\x00\x00\x3e\x00\x00\x38\x00\x00\x20\x00\x00\x00\x00\x00'\
    b'\x00\x00\x00\x00\x00\x00\x00\x00\x00\x00\x00\x00\x00\x00\x00\x00'\
    b'\x00\x00\x00\x00\x00\x00\x00\x00\x00\x00\x00\x00\x00\x00\x00\x00'\
    b'\x00\x00\x00\x00\x00\x00\x00\x00\x00\x00\x00\x00\x00\x00\x00\x00'\
    b'\x00\x00\x00\x00\x00\x00\x00\x00\x00\x00\x00\x00\x00\x00\x00\x00'\
    b'\x00\x1f\xff\xf8\x1f\xff\xf8\x1f\xff\xf8\x00\x00\x00\x00\x00\x00'\
    b'\x00\x00\x00\x1f\xff\xf8\x1f\xff\xf8\x1f\xff\xf8\x00\x00\x00\x00'\
    b'\x00\x00\x00\x00\x00\x00\x00\x00\x00\x00\x00\x00\x00\x00\x00\x00'\
    b'\x00\x00\x00\x00\x00\x00\x00\x00\x00\x00\x00\x00\x00\x00\x00\x00'\
    b'\x00\x00\x00\x00\x00\x00\x00\x00\x00\x00\x00\x00\x00\x00\x00\x00'\
    b'\x00\x00\x00\x00\x00\x00\x00\x00\x00\x00\x00\x00\x00\x00\x20\x00'\
    b'\x00\xe0\x00\x03\xe0\x00\x03\xe0\x00\x03\xe0\x00\x03\xe0\x00\x03'\
    b'\xe0\x00\x03\xe0\x00\x03\xe0\x00\x03\x80\x00\x7e\x00\x07\xe0\x00'\
    b'\x7c\x00\x07\xc0\x00\xfc\x00\x0f\xc0\x00\x3c\x00\x00\x80\x00\x00'\
    b'\x00\x00\x00\x00\x00\x00\x00\x00\x00\x00\x00\x00\x00\x00\x00\x00'\
    b'\x00\x00\x00\x00\x00\x00\x00\x00\x00\x00\x00\x00\x00\x00\x00\x00'\
    b'\x00\x00\x00\x00\x00\x00\x00\xff\xc0\x00\x00\x3f\xff\x80\x00\x07'\
    b'\xff\xff\x00\x00\x7e\x01\xfc\x00\x0f\xc0\x01\xf0\x00\xf8\x00\x03'\
    b'\xc0\x07\x80\x00\x0f\x00\x78\x0f\x0e\x3c\x07\x81\xfe\x70\xe0\x38'\
    b'\x1f\xfb\x87\x03\xc1\xe0\xf8\x1c\x1c\x1e\x03\xc0\xe0\xe1\xe0\x0e'\
    b'\x07\x0e\x0e\x00\x70\x38\x70\x70\x03\x81\xc3\x87\x00\x1c\x0e\x1c'\
    b'\x38\x00\xc0\xf0\xe1\xc0\x06\x07\x07\x0e\x00\x70\x38\x38\x70\x03'\
    b'\x83\x81\xc3\x80\x38\x3c\x0f\x0e\x03\xc3\xc0\x38\x78\x7f\x7c\x01'\
    b'\xc1\xff\x7f\xc0\x0f\x07\xf3\xfc\x00\x3c\x1f\x0f\x83\x80\xf0\x00'\
    b'\x00\x38\x07\xc0\x00\x07\x80\x1f\x80\x00\x78\x00\x3f\x80\x1f\x80'\
    b'\x00\xff\xff\xf8\x00\x01\xff\xff\x00\x00\x01\xff\xc0\x00\x00\x00'\
    b'\x00\x00\x00\x00\x00\x00\x00\x00\x00\x00\x00\x00\x00\x00\x00\x0c'\
    b'\x30\x06\x18\x03\x0c\x03\x8e\x01\x86\x00\xc3\x00\x61\x87\xff\xfb'\
    b'\xff\xfc\x0c\x30\x06\x18\x06\x18\x03\x0c\x1f\xff\xef\xff\xf0\xc3'\
    b'\x00\x61\x80\x30\xc0\x38\xe0\x18\x60\x0c\x30\x06\x18\x00\x00\x00'\
    b'\x00\x00\x00\x00\x00\x00\x00\x00\x00\x00\x00\x00\x00\x00\x00\x00'\
    b'\x00\x00\x00\x00\x00\x00\x00\x00\x00\x00\x00\x00\x00\x00\x00\x00'\
    b'\x00\x00\x00\x00\x00\x00\x00\x00\x00\x00\x00\x00\x00\x00\x00\x00'\
    b'\x00\x00\x00\x00\x00\x00\x00\x00\x01\xe0\x02\x1f\xe0\x1c\xff\xf0'\
    b'\xe3\x87\xff\x9c\x07\xf8\x70\x07\xc0\x80\x00\x00\x00\x00\x00\x00'\
    b'\x00\x00\x00\x00\x00\x00\x00\x00\x00\x00\x00\x00\x00\x00\x00\x00'\
    b'\x00\x00\x00\x00\x00\x00\x00\x00\x00\x00\x00\x00\x00\x00\x00\x00'\
    b'\x00\x00\x00\x00\x00\x00\x00\x00\x00\x00\x00\x00\x00\x00\x00\x00'\
    b'\x00\x00\xc0\x03\xc0\x07\x80\x19\x80\x33\x00\xc3\x01\x86\x02\x0c'\
    b'\x0c\x0c\x18\x18\x60\x18\xc0\x33\x00\x30\x00\x00\x00\x00\x00\x00'\
    b'\x00\x00\x00\x00\x00\x00\x00\x00\x00\x00\x00\x00\x00\x00\x00\x00'\
    b'\x00\x00\x00\x00\x00\x00\x00\x00\x00\x00\x00\x00\x00\x00\x00\x00'\
    b'\x00\x00\x00\x00\x18\x00\x03\x00\x01\xf8\x00\xff\xc0\x3f\xfc\x07'\
    b'\x33\x81\xe6\x38\x38\xc2\x07\x18\x00\xe3\x00\x1e\x60\x01\xec\x00'\
    b'\x1f\x80\x01\xfc\x00\x0f\xe0\x00\xfe\x00\x19\xe0\x03\x1e\x00\x61'\
    b'\xc6\x0c\x38\xe1\x87\x0f\x33\xe0\xff\xf8\x0f\xfe\x00\x7f\x00\x03'\
    b'\x00\x00\x60\x00\x0c\x00\x00\x00\x00\x00\x00\x00\x00\x00\x00\x00'\
    b'\x00\x00\x00\x00\x00\x00\x00\x00\x00\x0e\x01\xc0\x38\x07\x00\xe0'\
    b'\x1c\x03\x80\x70\x0e\x01\xc0\x38\x07\x00\xe0\x1c\x03\x80\x70\x00'\
    b'\x00\x00\x00\x06\x00\xe0\x1c\x03\x00\x00\x00\x00\x00\x00\x00\x00'\
    b'\x00\x00\x00\x00\x00\x00\x00\x00\x00\x00\x00\x00\x00\x00\x00\xf8'\
    b'\x07\xf8\x3f\xe1\xe3\xc7\x07\x1c\x1c\x70\x70\x01\xc0\x0e\x00\x38'\
    b'\x01\xc0\x0f\x00\x38\x01\xe0\x07\x00\x1c\x00\x70\x00\x00\x00\x00'\
    b'\x08\x00\x70\x01\xc0\x02\x00\x00\x00\x00\x00\x00\x00\x00\x00\x00'\
    b'\x00\x00\x00\x00\x00\x00\x00\x00\x00\x00\x00\x00\x00\x00\x00\x00'\
    b'\x00\x00\x00\x00\x00\x00\x00\x00\x00\x00\x00\x00\x00\x00\x00\x00'\
    b'\x00\x00\x00\x00\x00\x00\x00\x00\x1c\x00\x00\x1c\x00\x00\x1c\x00'\
    b'\x00\x1c\x00\x00\x1c\x00\x00\x1c\x00\x00\x1c\x00\x00\x1c\x00\x1f'\
    b'\xff\xfc\x1f\xff\xfc\x1f\xff\xfc\x00\x1c\x00\x00\x1c\x00\x00\x1c'\
    b'\x00\x00\x1c\x00\x00\x1c\x00\x00\x1c\x00\x00\x1c\x00\x00\x1c\x00'\
    b'\x00\x00\x00\x00\x00\x00\x00\x00\x00\x00\x00\x00\x00\x00\x00\x00'\
    b'\x00\x00\x00\x00\x00\x00\x00\x00\x00\x00\x00\x00\x00\x00\x00\x00'\
    b'\x00\x00\x00\x00\x00\x00\x00\x00\x00\x00\x00\x00\x00\x00\x00\x00'\
    b'\x00\x00\x00\x07\x01\xe0\x38\x0f\x01\xc0\x30\x0e\x01\x80\x00\x00'\
    b'\x00\x00\x00\x00\x00\x00\x00\x00\x00\x00\x00\x00\x00\x00\x00\x00'\
    b'\x00\x00\x00\x00\x00\x00\x00\x00\x00\x00\x00\x00\x1f\xe3\xfc\x7f'\
    b'\x80\x00\x00\x00\x00\x00\x00\x00\x00\x00\x00\x00\x00\x00\x00\x00'\
    b'\x00\x00\x00\x00\x00\x00\x00\x00\x00\x00\x00\x00\x00\x00\x00\x00'\
    b'\x00\x00\x00\x00\x00\x00\x00\x00\x00\x00\x20\x0e\x01\xc0\x10\x00'\
    b'\x00\x00\x00\x00\x00\x00\x00\x00\x00\x00\x00\x00\x40\x1c\x03\x80'\
    b'\x20\x00\x00\x00\x00\x00\x00\x00\x00\x00\x00\x00\x00\x00\x00\x00'\
    b'\x00\x00\x00\x00\x00\x00\x00\x00\x00\x00\x00\x00\x00\x00\x00\x00'\
    b'\x00\x00\x00\x00\x00\x00\x00\x00\x00\x00\x00\x00\x00\x00\x00\x80'\
    b'\x38\x07\x00\x40\x00\x00\x00\x00\x00\x00\x00\x00\x00\x00\x00\x00'\
    b'\x00\x00\x01\x80\x06\x00\x0c\x00\x38\x00\x60\x00\xc0\x03\x80\x06'\
    b'\x00\x0c\x00\x30\x00\x60\x01\xc0\x03\x00\x06\x00\x18\x00\x30\x00'\
    b'\x60\x01\x80\x03\x00\x0e\x00\x18\x00\x30\x00\xc0\x01\x80\x07\x00'\
    b'\x0c\x00\x18\x00\x60\x00\xc0\x01\x80\x06\x00\x00\x00\x00\x00\x00'\
    b'\x00\x00\x00\x00\x00\x00\x00\x00\x00\x00\x00\x00\x00\x00\x00\x00'\
    b'\x00\x00\x00\x00\x00\x00\x00\x1c\x03\xf0\x1c\x07\xe0\x1c\x0f\xe0'\
    b'\x18\x03\xc0\x38\x03\x80\x38\x07\x00\x30\x0e\x00\x70\x1c\x03\xf0'\
    b'\x38\x0f\xf0\x60\x3c\xe1\xc0\x70\xff\x01\xc1\xfc\x03\x81\xe0\x07'\
    b'\x01\xc0\x0e\x01\xc0\x1c\x03\x80\x38\x03\x80\x70\x03\x80\xe0\x07'\
    b'\x81\xfc\x07\x03\xf8\x07\x03\xf0\x07\x00\x00\x00\x00\x00\x00\x00'\
    b'\x00\x00\x00\x00\x00\x00\x00\x00\x00\x00\x00\x00\x00\x00\x00\x00'\
    b'\x00\x00\x00\x00\x00\x00\x00\x00\x00\x00\x00\x00\x00\x00\x00\x00'\
    b'\xff\xf0\x07\xff\xc0\x3f\xfe\x00\x00\x78\x00\x01\xc0\x00\x0e\x00'\
    b'\x00\x70\x00\x03\x80\x00\x1c\x00\x00\xe0\x00\x07\x00\x00\x38\x00'\
    b'\x01\xc0\x00\x0e\x00\x00\x70\x00\x03\x80\x00\x1c\x00\x00\xe0\x00'\
    b'\x07\x00\x00\x38\x1f\xff\xf8\xff\xff\xc7\xff\xfe\x00\x00\x00\x00'\
    b'\x00\x00\x00\x00\x00\x00\x00\x00\x00\x00\x00\x00\x00\x00\x00\x00'\
    b'\x00\x00\x00\x00\x00\x00\x00\x00\x00\x00\x00\x00\x00\x01\xfe\x00'\
    b'\xff\x00\x7f\x80\x01\xc0\x00\xe0\x00\x70\x00\x38\x00\x1c\x00\x0e'\
    b'\x00\x07\x00\x03\x80\x01\xc0\x00\xe0\x00\xf0\x00\x78\x00\x7c\x00'\
    b'\x7e\x00\x77\x00\x73\x80\xf1\xc1\xf0\xe0\xf0\x70\x60\x38\x00\x00'\
    b'\x00\x00\x00\x00\x00\x00\x00\x00\x00\x00\x00\x00\x00\x00\x00\x00'\
    b'\x00\x00\x00\x00\x00\x00\x00\x00\x00\x00\x00\x00\x00\x03\xff\xfe'\
    b'\x7f\xff\xcf\xff\xf8\x00\xe0\x00\x1c\x00\x03\x80\x00\x70\x00\x0e'\
    b'\x00\x01\xc0\x00\x38\x00\x07\x00\x00\xe0\x00\x1c\x00\x03\x80\x00'\
    b'\x70\x00\x0e\x00\x01\xc0\x00\x38\x00\x07\x00\x00\xe0\x00\x1c\x00'\
    b'\x03\x80\x00\x70\x00\x00\x00\x00\x00\x00\x00\x00\x00\x00\x00\x00'\
    b'\x00\x00\x00\x00\x00\x00\x00\x00\x00\x00\x00\x00\x00\x00\x00\x00'\
    b'\x00\x00\x00\x00\x00\x00\x00\x00\x00\x3f\xff\xf0\x7f\xff\xe0\xff'\
    b'\xff\xc0\x00\x03\x80\x00\x07\x00\x00\x0e\x00\x00\x1c\x00\x00\x38'\
    b'\x1c\x00\x70\x38\x00\xe0\x70\x01\xc0\xe0\x03\x81\xc0\x07\x03\x80'\
    b'\x0e\x07\x00\x1c\x0e\x00\x38\x1c\x00\x70\x38\x00\xe0\x70\x01\xc0'\
    b'\xe0\x03\x81\xc0\x07\x03\x80\x0e\x07\x00\x1c\x00\x00\x00\x00\x00'\
    b'\x00\x00\x00\x00\x00\x00\x00\x00\x00\x00\x00\x00\x00\x00\x00\x00'\
    b'\x00\x00\x00\x00\x00\x00\x00\x00\x00\x00\x03\xfe\x1f\xf0\xff\x80'\
    b'\x1c\x00\xe0\x07\x00\x38\x01\xc0\x0e\x00\x70\x03\x80\x1c\x00\xe0'\
    b'\x07\x00\x38\x01\xc0\x0e\x00\x70\x03\x80\x1c\x00\xe0\x07\x00\x38'\
    b'\x00\x00\x00\x00\x00\x00\x00\x00\x00\x00\x00\x00\x00\x00\x00\x00'\
    b'\x00\x00\x00\x00\x00\x01\xff\xdf\xfd\xff\xc1\xc0\x1c\x01\xc0\x1c'\
    b'\x01\xc0\x1c\x01\xc0\x1c\x01\xc0\x1c\x01\xc0\x1c\x01\xc0\x1c\x01'\
    b'\xc0\x1c\x01\xc0\x1c\x01\xc0\x1c\x00\x00\x00\x00\x00\x00\x00\x00'\
    b'\x00\x00\x00\x00\x00\x00\x00\x00\x00\x00\x00\x00\x00\x00\x00\x00'\
    b'\x00\x00\x00\x00\x00\x00\x3f\xff\xe0\xff\xff\x83\xff\xfe\x01\xc0'\
    b'\x38\x07\x00\xe0\x1c\x03\x80\x70\x0e\x01\xc0\x38\x07\x00\xe0\x1c'\
    b'\x03\x80\x70\x0e\x01\xc0\x38\x07\x00\xe0\x1c\x03\x80\x70\x0e\x01'\
    b'\xc0\x38\x07\x00\xe0\x1c\x03\x80\x70\x0e\x01\xc0\x38\x07\x00\xe0'\
    b'\x1c\x03\x80\x70\x0e\x00\x00\x00\x00\x00\x00\x00\x00\x00\x00\x00'\
    b'\x00\x00\x00\x00\x00\x00\x00\x00\x00\x00\x00\x00\x00\x00\x00\x00'\
    b'\x00\x00\x00\x00\x00\x00\x00\x00\x00\x00\x00\x00\x7c\x1f\x01\xf1'\
    b'\xfe\x07\xc7\xf8\x07\x3c\xf0\x1c\xe1\xc0\x73\x87\x01\xce\x1c\x07'\
    b'\x38\x70\x1c\xe1\xc0\x70\x07\x01\xc0\x1c\x07\x00\x70\x1c\x01\xc0'\
    b'\x70\x07\x01\xc0\x1c\x07\x00\x70\x1c\x01\xc0\x70\x07\x01\xe0\x1c'\
    b'\x07\xc0\xf0\x0f\xff\xc0\x1f\xfe\x00\x1f\xe0\x00\x00\x00\x00\x00'\
    b'\x00\x00\x00\x00\x00\x00\x00\x00\x00\x00\x00\x00\x00\x00\x00\x00'\
    b'\x00\x00\x00\x00\x00\x00\x00\x00\x00\x01\xff\x0f\xf8\x7f\xc0\x0e'\
    b'\x00\x70\x03\x80\x1c\x00\xe0\x07\x00\x38\x01\xc0\x00\x00\x00\x00'\
    b'\x00\x00\x00\x00\x00\x00\x00\x00\x00\x00\x00\x00\x00\x00\x00\x00'\
    b'\x00\x00\x00\x00\x00\x00\x00\x00\x00\x00\x00\x00\x00\x00\x00\x00'\
    b'\x00\x00\x00\x00\x00\x00\x00\x00\x00\x00\x00\x00\x00\x7f\xfc\x03'\
    b'\xff\xf0\x1f\xff\xc0\x00\x1f\x00\x00\x78\x00\x01\xc0\x00\x0e\x00'\
    b'\x00\x70\x00\x03\x80\x00\x1c\x00\x00\xe0\x00\x07\x00\x00\x38\x00'\
    b'\x01\xc0\x00\x0e\x00\x00\x70\x00\x03\x80\x00\x1c\x00\x00\xe0\x00'\
    b'\x0f\x07\xff\xf0\x3f\xff\x81\xff\xf0\x00\x00\x00\x00\x00\x00\x00'\
    b'\x00\x00\x00\x00\x00\x00\x00\x00\x00\x00\x00\x00\x00\x00\x00\x00'\
    b'\x00\x00\x00\x00\x00\x00\x00\x00\x00\x00\x00\x00\x1f\xff\x83\xff'\
    b'\xf0\x7f\xfe\x00\x01\xc0\x00\x38\x00\x07\x00\x00\xe0\x00\x1c\x00'\
    b'\x03\x80\x00\x70\x00\x0e\x00\x01\xc0\x00\x38\x00\x07\x00\x00\xe0'\
    b'\x00\x1c\x00\x03\x80\x00\x70\x00\x0e\x00\x01\xc0\x00\x38\x00\x07'\
    b'\x00\x00\xe0\x00\x1c\x00\x03\x80\x00\x70\x00\x0e\x00\x01\xc0\x00'\
    b'\x00\x00\x00\x00\x00\x00\x00\x00\x00\x00\x00\x0e\x00\x00\x70\x00'\
    b'\x03\x80\x00\x1c\x00\x00\xff\xff\x07\xff\xfc\x1f\xff\xe0\x00\x07'\
    b'\x00\x00\x38\x00\x01\xc0\x00\x0e\x00\x00\x70\x00\x03\x80\x00\x1c'\
    b'\x00\x01\xe0\x00\x1f\x00\x01\xf0\x00\x1f\x00\x01\xf0\x00\x0f\x00'\
    b'\x00\xf0\x00\x0f\x00\x00\xf0\x00\x07\x00\x00\x38\x00\x01\xc0\x00'\
    b'\x0e\x00\x00\x00\x00\x00\x00\x00\x00\x00\x00\x00\x00\x00\x00\x00'\
    b'\x00\x00\x00\x00\x00\x00\x00\x00\x00\x00\x00\x00\x00\x00\x00\x00'\
    b'\x00\x00\x00\x00\x00\x00\x00\x00\xf8\x3e\x03\xf3\xfe\x0f\xdf\xf8'\
    b'\x07\xe0\xf0\x1f\x01\xc0\x78\x07\x01\xe0\x1c\x07\x00\x70\x1c\x01'\
    b'\xc0\x70\x07\x01\xc0\x1c\x07\x00\x70\x1c\x01\xc0\x70\x07\x01\xc0'\
    b'\x1c\x07\x00\x70\x1c\x01\xc0\x70\x07\x01\xc0\x1c\x07\x00\x70\x1c'\
    b'\x3f\xc0\x70\xff\x01\xc3\xf8\x00\x00\x00\x00\x00\x00\x00\x00\x00'\
    b'\x00\x00\x00\x00\x00\x00\x00\x00\x00\x00\x00\x00\x00\x00\x00\x00'\
    b'\x00\x00\x00\x00\x00\x00\x00\x00\x00\x00\x00\x00\x00\x03\xff\xfe'\
    b'\x0f\xff\xfc\x3f\xff\xf0\x1c\x01\xc0\x70\x07\x01\xc0\x1c\x07\x00'\
    b'\x70\x1c\x01\xc0\x70\x07\x01\xc0\x1c\x07\x00\x70\x1c\x01\xc0\x70'\
    b'\x07\x01\xc0\x1c\x07\x00\x70\x1c\x01\xc0\x70\x07\x01\xc0\x1c\x07'\
    b'\x00\x70\x1c\x01\xc0\x7f\xff\x01\xff\xfc\x03\xff\xf0\x00\x00\x00'\
    b'\x00\x00\x00\x00\x00\x00\x00\x00\x00\x00\x00\x00\x00\x00\x00\x00'\
    b'\x00\x00\x00\x00\x00\x00\x00\x00\x00\x00\x00\x01\xf8\x0f\xe0\x7f'\
    b'\x00\x38\x01\xc0\x0e\x00\x70\x03\x80\x1c\x00\xe0\x07\x00\x38\x01'\
    b'\xc0\x0e\x00\x70\x03\x80\x1c\x00\xe0\x07\x00\x38\x3f\xc1\xfe\x0f'\
    b'\xe0\x00\x00\x00\x00\x00\x00\x00\x00\x00\x00\x00\x00\x00\x00\x00'\
    b'\x00\x00\x00\x00\x00\x00\xfe\x1f\xc3\xf8\x07\x00\xe0\x1c\x03\x80'\
    b'\x70\x0e\x01\xc0\x38\x07\x00\xe0\x1c\x03\x80\x70\x0e\x01\xc0\x38'\
    b'\x07\x00\xe0\x1c\x03\x80\x70\x0e\x01\xc0\x38\x07\x00\x00\x00\x00'\
    b'\x00\x00\x00\x00\x00\x00\x00\x00\x00\x00\x00\x00\x00\x00\x00\x00'\
    b'\x00\x03\xff\xf8\x1f\xff\xe0\xff\xff\x01\xc0\x38\x0e\x01\xc0\x70'\
    b'\x0e\x03\x80\x70\x1c\x03\x80\xe0\x1c\x07\x00\xe0\x38\x07\x01\xc0'\
    b'\x38\x0e\x01\xc0\x70\x0e\x03\x80\x70\x1c\x03\x80\xe0\x1c\x07\x00'\
    b'\xe0\x3c\x0f\x01\xf0\xf8\x07\xff\x80\x1f\xf8\x00\x3f\x00\x00\x00'\
    b'\x00\x00\x00\x00\x00\x00\x00\x00\x00\x00\x00\x00\x00\x00\x00\x00'\
    b'\x00\x00\x00\x00\x00\x00\x00\x00\x00\x00\x00\x00\x00\x00\x00\x00'\
    b'\x00\x00\x00\x07\xf1\xfc\x1f\xc7\xf0\x7f\x1f\xc0\x1c\x07\x00\x70'\
    b'\x1c\x01\xc0\x70\x07\x01\xc0\x1c\x07\x00\x70\x1c\x01\xc0\x70\x07'\
    b'\x01\xc0\x1c\x07\x00\x70\x1c\x01\xc0\x70\x07\x01\xc0\x1c\x07\x00'\
    b'\x70\x1c\x01\xc0\xf0\x07\x03\x80\x1c\x3e\x07\xff\xf0\x1f\xff\x80'\
    b'\x7f\xf0\x00\x00\x00\x00\x00\x00\x00\x00\x00\x00\x00\x00\x00\x00'\
    b'\x00\x00\x00\x00\x00\x00\x00\x00\x00\x00\x00\x00\x00\x00\x00\x00'\
    b'\x00\x00\x00\x00\x00\x00\x00\x00\x01\xff\xf0\x1f\xff\xc0\xff\xfe'\
    b'\x07\x00\x70\x38\x03\x81\xc0\x1c\x0e\x00\xe0\x70\x07\x03\x80\x38'\
    b'\x1c\x01\xc0\xe0\x0e\x07\xf8\x70\x3f\xc3\x81\xfe\x1c\x00\x00\xe0'\
    b'\x00\x07\x00\x00\x38\x00\x01\xc0\x00\x0e\x00\x00\xf0\x3f\xff\x81'\
    b'\xff\xf8\x0f\xff\x80\x00\x00\x00\x00\x00\x00\x00\x00\x00\x00\x00'\
    b'\x00\x00\x00\x00\x00\x00\x00\x00\x00\x00\x00\x00\x00\x00\x00\x00'\
    b'\x00\x00\x00\x00\x00\x00\x00\x00\x00\x01\xff\xf0\x1f\xff\xc0\xff'\
    b'\xfe\x07\x00\x70\x38\x03\x81\xc0\x1c\x0e\x00\xe0\x70\x07\x03\x80'\
    b'\x38\x1c\x01\xc0\xe0\x0e\x07\x00\x70\x3f\xc3\x81\xfe\x1c\x0f\xf0'\
    b'\xe0\x00\x07\x00\x00\x38\x00\x01\xc0\x00\x0e\x00\x00\x70\x00\x03'\
    b'\x80\x00\x1c\x00\x00\xe0\x00\x07\x00\x00\x38\x00\x01\xc0\x00\x0e'\
    b'\x00\x00\x70\x00\x00\x00\x00\x00\x00\x00\x00\x00\x00\x00\x00\x00'\
    b'\x00\x00\x00\x00\x00\x00\x00\x00\x00\x00\x03\xf8\x7e\x1f\xc3\xf8'\
    b'\xfe\x1f\xc0\x70\x0e\x03\x80\x70\x1c\x03\x80\xe0\x38\x07\x83\xc0'\
    b'\x1c\x3c\x00\x73\xe0\x01\xfe\x00\x07\xe0\x00\x1e\x00\x00\x3c\x00'\
    b'\x00\xf0\x00\x03\xc0\x00\x0e\x00\x00\x38\x00\x01\xc0\x00\x0e\x1f'\
    b'\xff\xf0\xff\xff\x87\xff\xf8\x00\x00\x00\x00\x00\x00\x00\x00\x00'\
    b'\x00\x00\x00\x00\x00\x00\x00\x00\x00\x00\x00\x00\x00\x00\x00\x00'\
    b'\x00\x00\x00\x00\x00\x00\x00\x00\x00\x00\x01\xf8\x0f\x9f\xc0\xfd'\
    b'\xfc\x0f\xc1\xc0\x1c\x1c\x01\xc1\xc0\x1c\x1c\x03\x81\xc0\x38\x1c'\
    b'\x07\x01\xc1\xf0\x1c\x7e\x01\xff\xc0\x1f\xf0\x01\xfc\x00\x1c\x00'\
    b'\x01\xc0\x00\x1c\x00\x01\xc0\x00\x1c\x00\x01\xc0\x00\x1c\x00\x01'\
    b'\xc0\x00\x1c\x00\x01\xc0\x00\x1c\x00\x01\xc0\x00\x1c\x00\x01\xc0'\
    b'\x00\x00\x00\x00\x00\x00\x00\x00\x00\x00\x00\x00\x00\x00\x00\x00'\
    b'\x00\x00\x00\x00\x00\x00\x00\x00\x1f\xff\xf0\xff\xff\xc7\xff\xfe'\
    b'\x00\x00\x70\x00\x03\x80\x00\x1c\x00\x00\xe0\xe0\x07\x07\x00\x38'\
    b'\x38\x01\xc1\xc0\x1e\x0e\x00\xe0\x70\x0f\x03\x80\xf0\x1c\x0f\x00'\
    b'\xe0\x70\x07\x07\x80\x38\x78\x01\xc3\x80\x0e\x1c\x00\x70\xe0\x03'\
    b'\x87\x00\x1c\x38\x00\xe0\x00\x07\x00\x00\x38\x00\x01\xc0\x00\x0e'\
    b'\x00\x00\x00\x00\x00\x00\x00\x00\x00\x00\x00\x00\x00\x00\x00\x00'\
    b'\x00\x00\x00\x00\x00\x00\x00\x03\xff\xf8\x7f\xff\x0f\xff\xe0\x00'\
    b'\x1c\x00\x03\x80\x00\x70\x00\x0e\x00\x01\xc0\x00\x38\x00\x07\x00'\
    b'\x00\xe0\x00\x1c\x00\x03\x80\x00\x70\x00\x0e\x00\x01\xc0\x00\x38'\
    b'\x00\x07\x00\x00\xe0\x00\x1c\x00\x03\x80\x00\x70\x00\x0e\x00\x00'\
    b'\x00\x00\x00\x00\x00\x00\x00\x00\x00\x00\x00\x00\x00\x00\x00\x00'\
    b'\x00\x00\x00\x00\x00\x00\x00\x00\x00\x00\x00\x00\x00\x00\x00\x00'\
    b'\x00\x00\x00\x00\x00\x7c\x71\xf0\x3e\x38\xf8\x1f\x1c\x7c\x0e\x0e'\
    b'\x0e\x07\x07\x07\x03\x83\x83\x81\xc1\xc1\xc0\xe0\xe0\xe0\x70\x70'\
    b'\x70\x38\x38\x38\x1c\x1c\x1c\x0e\x0e\x0e\x07\x07\x07\x03\x83\x83'\
    b'\x81\xc1\xc1\xc0\xe0\xe0\xe0\x70\x70\x70\x38\x38\x38\x1c\x1c\x1c'\
    b'\x0e\x0e\x0e\x07\xff\xff\x01\xff\xff\x00\x7f\xff\x00\x00\x00\x00'\
    b'\x00\x00\x00\x00\x00\x00\x00\x00\x00\x00\x00\x00\x00\x00\x00\x00'\
    b'\x00\x00\x00\x00\x00\x00\x00\x00\x00\x00\x00\x00\x00\x00\x00\x00'\
    b'\x00\x00\x00\x00\x00\x00\x01\xff\xff\x83\xff\xff\x07\xff\xfe\x01'\
    b'\xc0\x1c\x03\x80\x38\x07\x00\x70\x0e\x00\xe0\x1c\x01\xc0\x38\x03'\
    b'\x80\x70\x07\x00\xe0\x0e\x01\xc0\x1c\x03\x80\x38\x07\x00\x70\x0e'\
    b'\x00\xe0\x1c\x01\xc0\x38\x03\x80\x70\x07\x00\xe0\x0e\x01\xc0\x1c'\
    b'\x1f\x80\x38\x3f\x00\x70\x7c\x00\xe0\x00\x00\x00\x00\x00\x00\x00'\
    b'\x00\x00\x00\x00\x00\x00\x00\x00\x00\x00\x00\x00\x00'

WIDTHS = memoryview(_WIDTHS)
OFFSETS = memoryview(_OFFSETS)
BITMAPS = memoryview(_BITMAPS)
